gallicchio/ai_unleashes_chaos/docs/images/lorenz-bottom.png

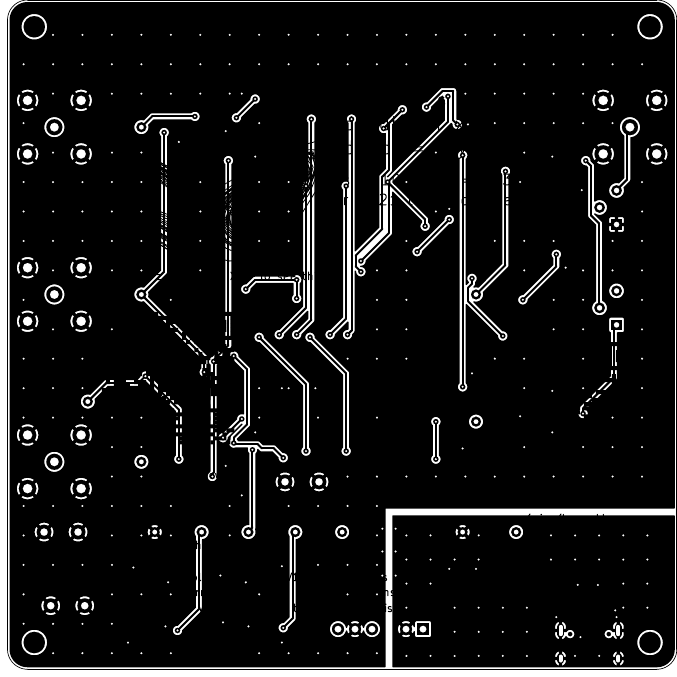
docs/images/lorenz-bottom.png
