gallicchio/ai_unleashes_chaos/docs/images/lorenz-silk-bottom.png

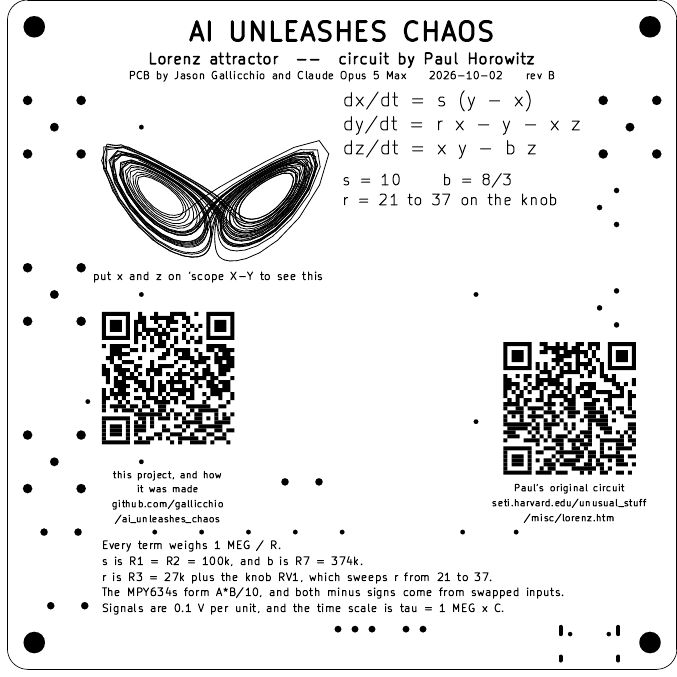
docs/images/lorenz-silk-bottom.png
