gallicchio/ai_unleashes_chaos/docs/images/lorenz-silk-top.png

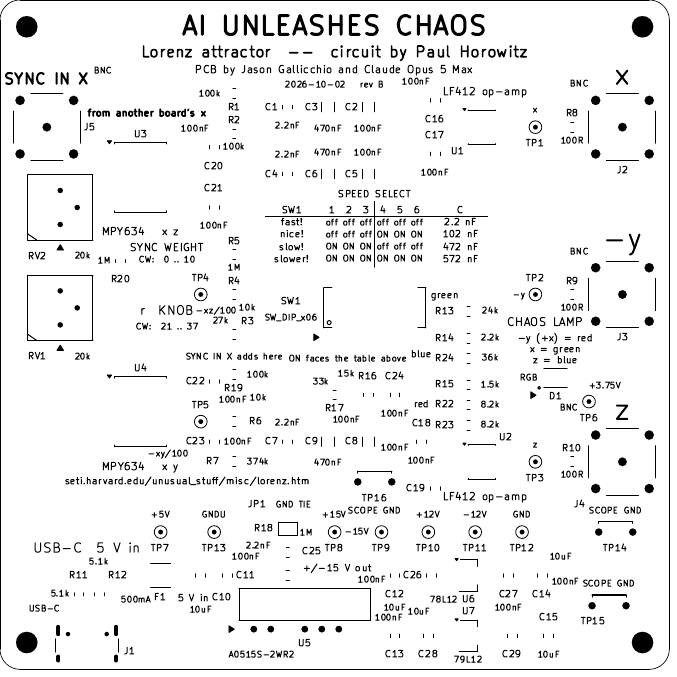
docs/images/lorenz-silk-top.png
