gallicchio/ai_unleashes_chaos/docs/images/lorenz-top.png

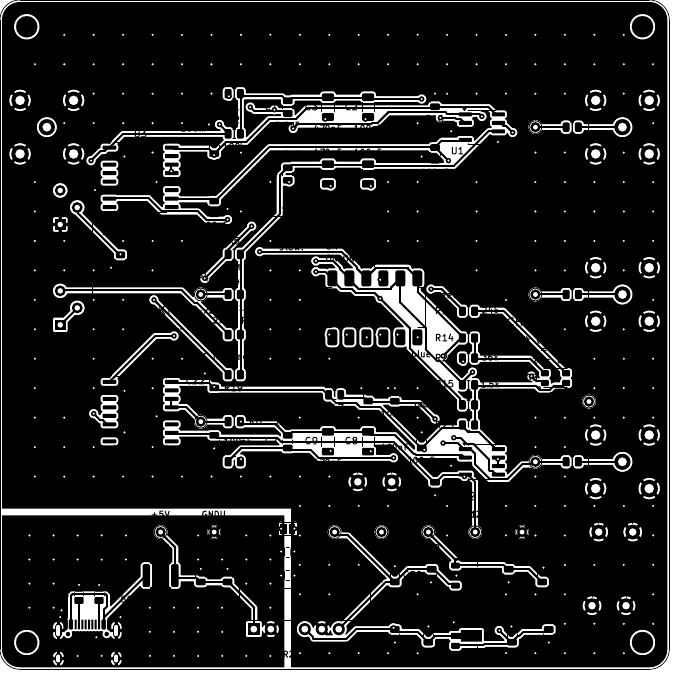
docs/images/lorenz-top.png
