gallicchio/ai_unleashes_chaos/docs/images/thumbnail_jason.png

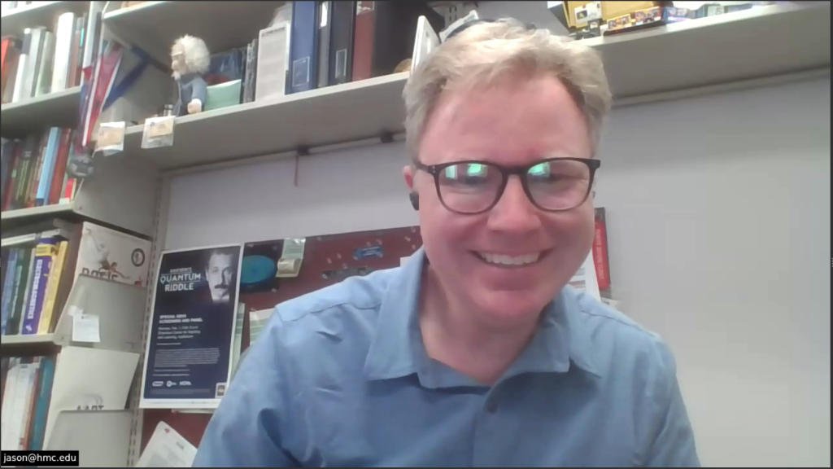
docs/images/thumbnail_jason.png
