gallicchio/ai_unleashes_chaos/docs/images/thumbnail_paul.png

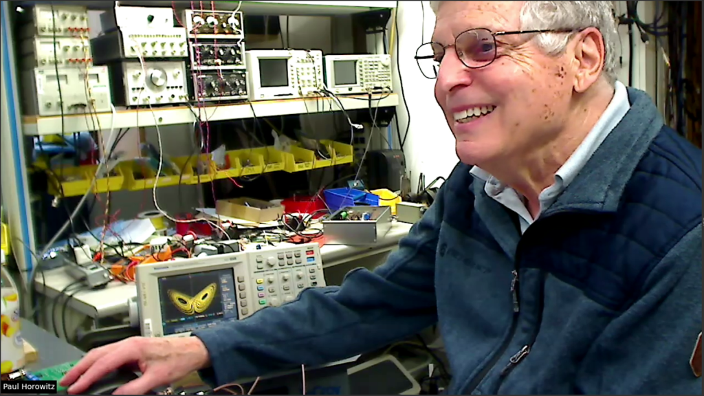
docs/images/thumbnail_paul.png
