gallicchio/ai_unleashes_chaos/docs/images/thumbnail_single.png

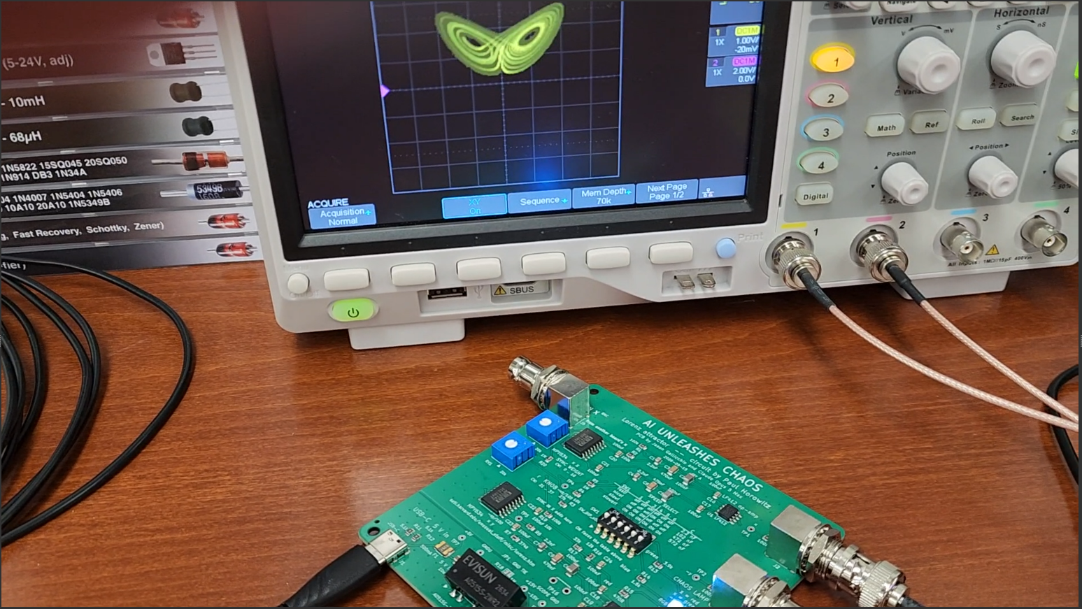
docs/images/thumbnail_single.png
