gallicchio/ai_unleashes_chaos/docs/images/thumbnail_sync.png

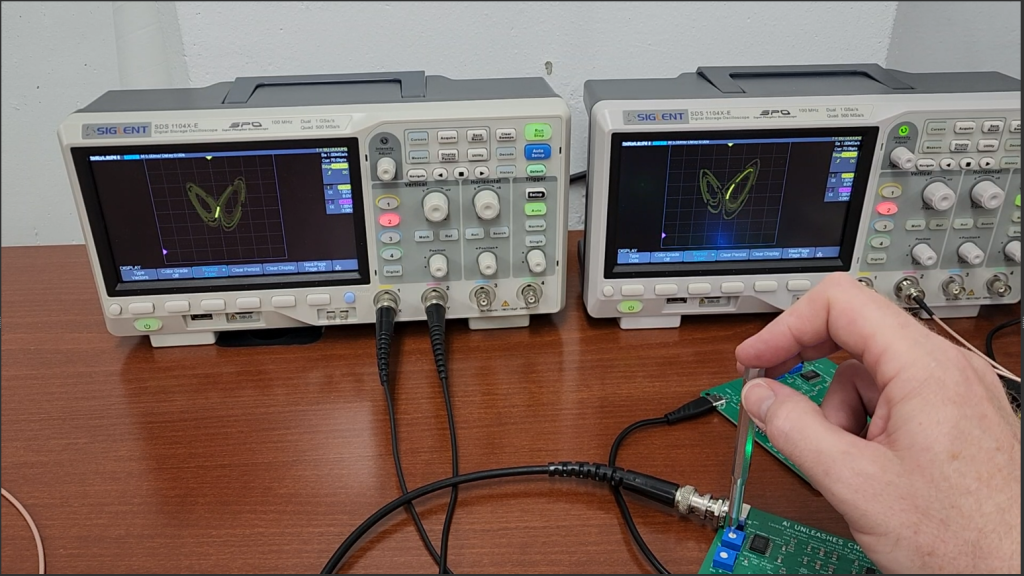
docs/images/thumbnail_sync.png
