gallicchio/ai_unleashes_chaos/docs/lamp/bestof/opt-038.png

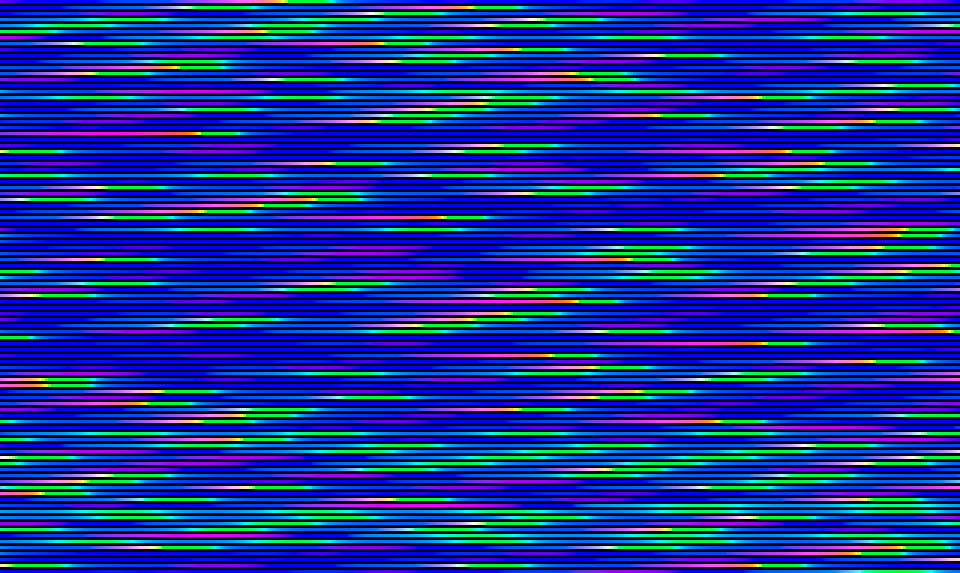
docs/lamp/bestof/opt-038.png
