gallicchio/ai_unleashes_chaos/docs/lamp/bestof/opt-054.png

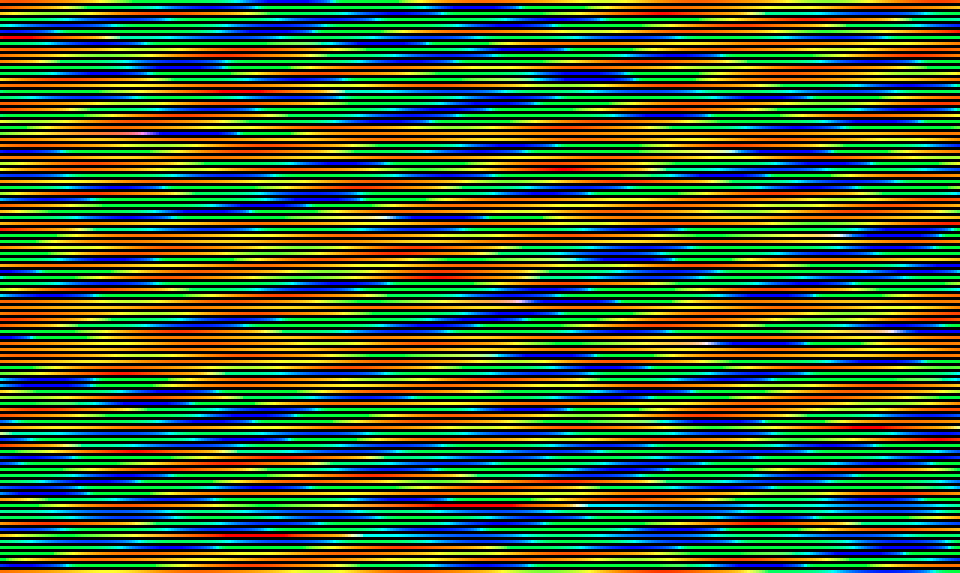
docs/lamp/bestof/opt-054.png
