gallicchio/ai_unleashes_chaos/docs/lamp/bestof/opt-065.png

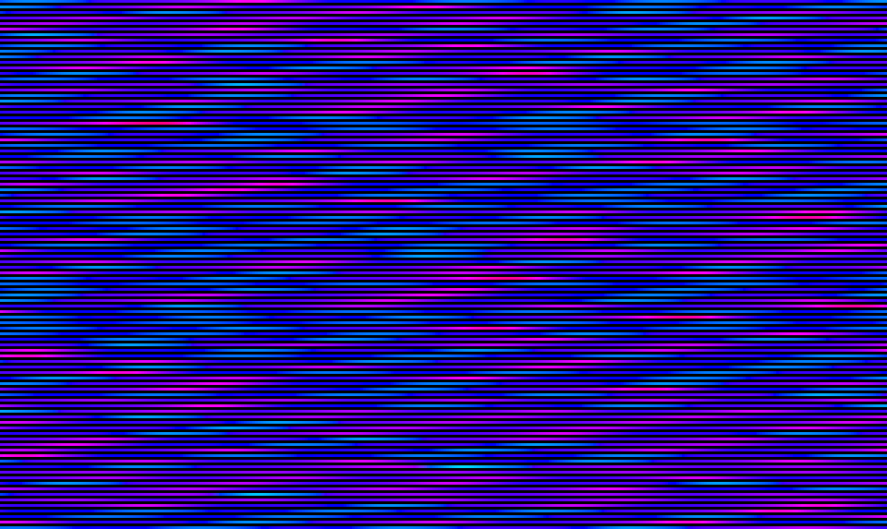
docs/lamp/bestof/opt-065.png
