gallicchio/ai_unleashes_chaos/docs/lamp/bestof/opt-072.png

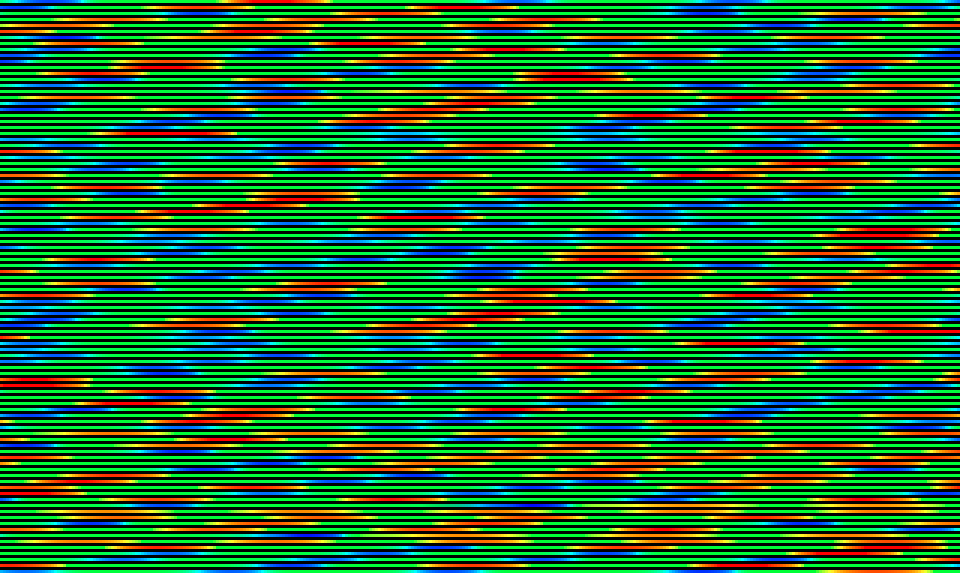
docs/lamp/bestof/opt-072.png
