gallicchio/ai_unleashes_chaos/docs/lamp/bestof/opt-088.png

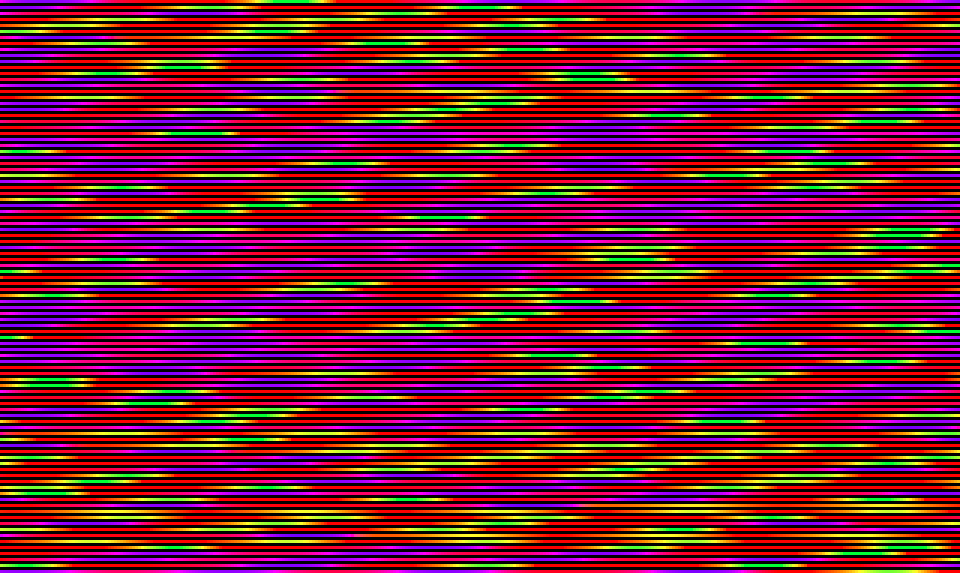
docs/lamp/bestof/opt-088.png
