gallicchio/ai_unleashes_chaos/docs/lamp/opt-001.png

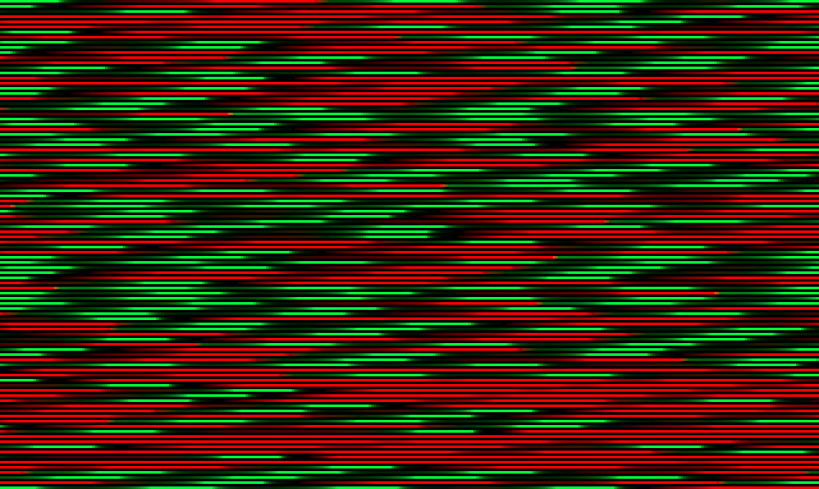
docs/lamp/opt-001.png
