gallicchio/ai_unleashes_chaos/docs/lamp/opt-002.png

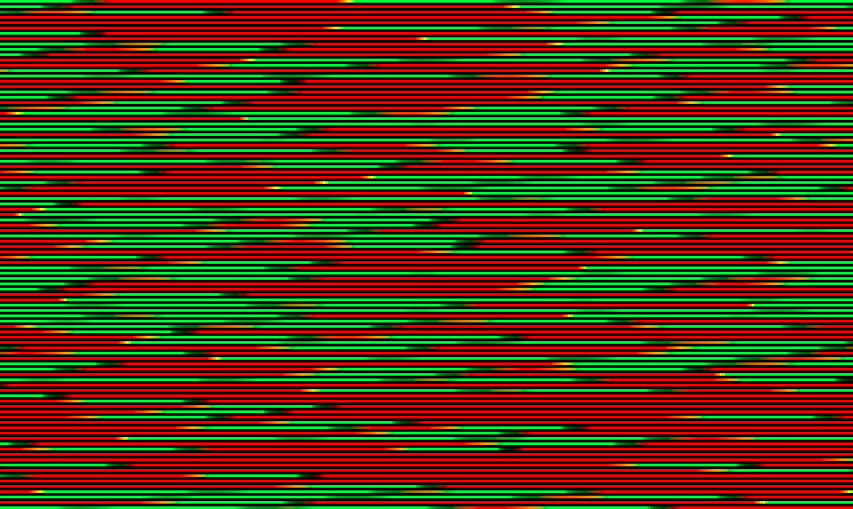
docs/lamp/opt-002.png
