gallicchio/ai_unleashes_chaos/docs/lamp/opt-003.png

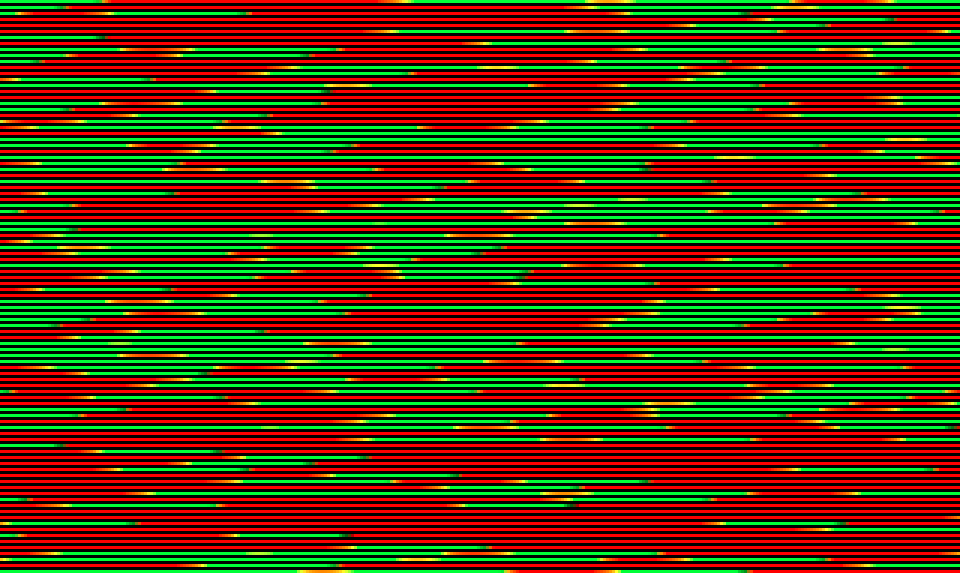
docs/lamp/opt-003.png
