gallicchio/ai_unleashes_chaos/docs/lamp/opt-004.png

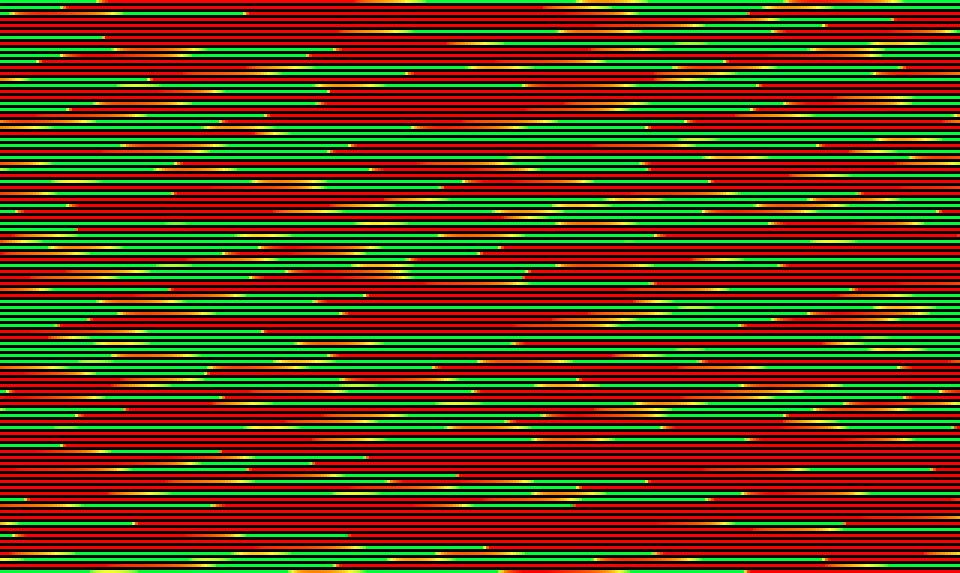
docs/lamp/opt-004.png
