gallicchio/ai_unleashes_chaos/docs/lamp/opt-006.png

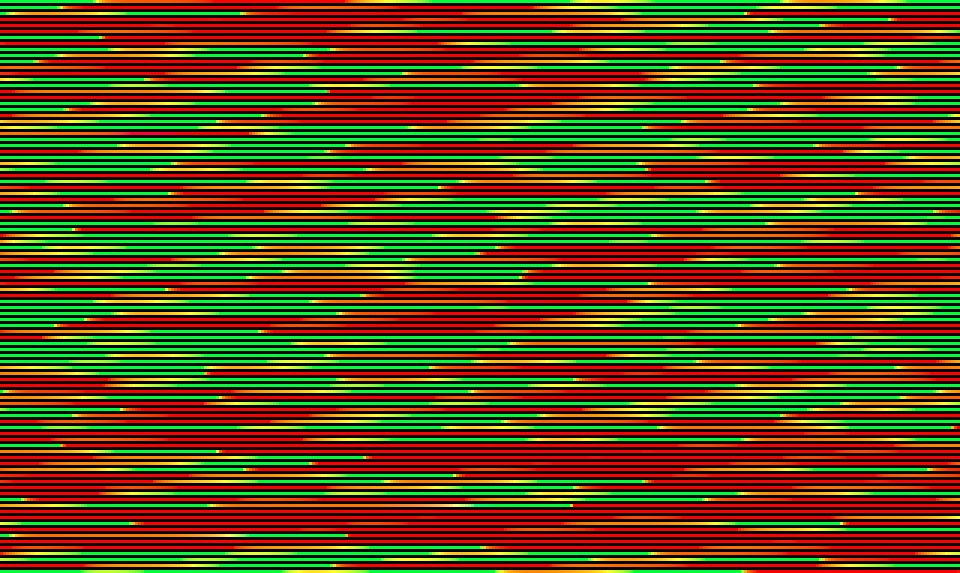
docs/lamp/opt-006.png
