gallicchio/ai_unleashes_chaos/docs/lamp/opt-007.png

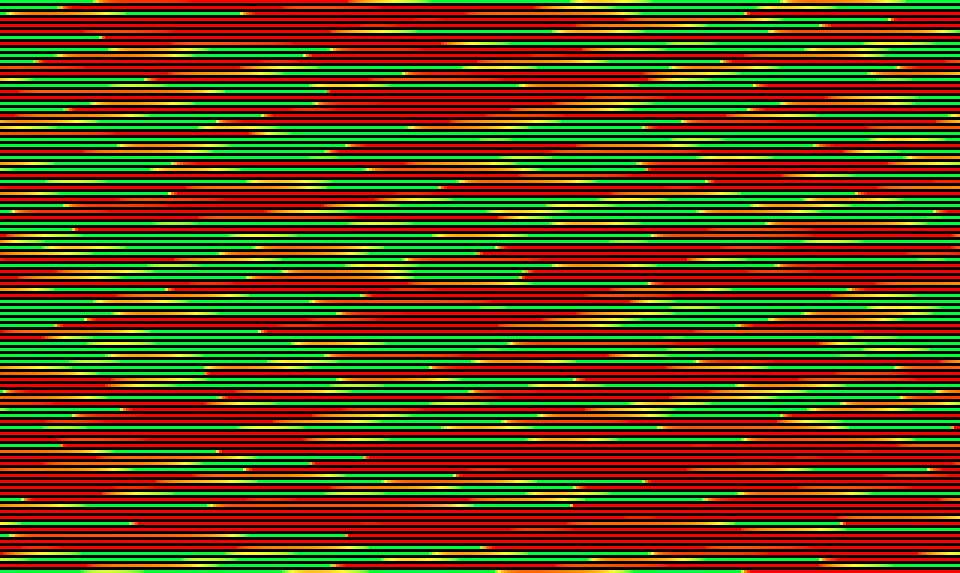
docs/lamp/opt-007.png
