gallicchio/ai_unleashes_chaos/docs/lamp/opt-008.png

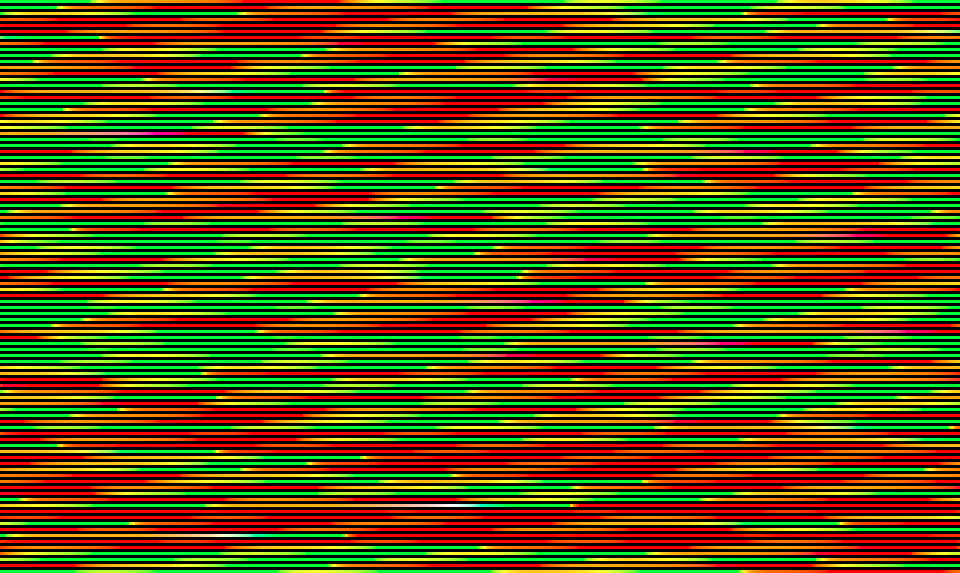
docs/lamp/opt-008.png
