gallicchio/ai_unleashes_chaos/docs/lamp/opt-010.png

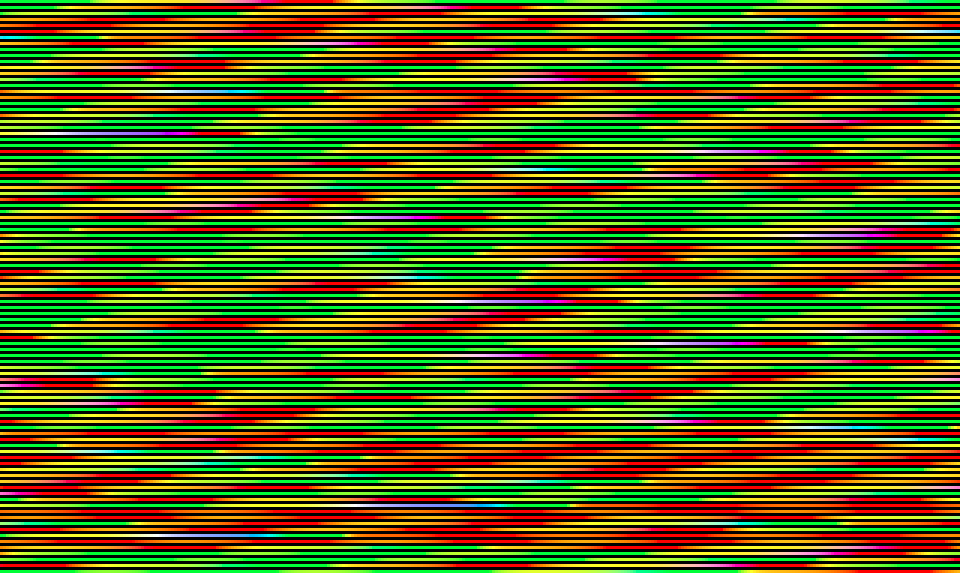
docs/lamp/opt-010.png
