gallicchio/ai_unleashes_chaos/docs/lamp/opt-011.png

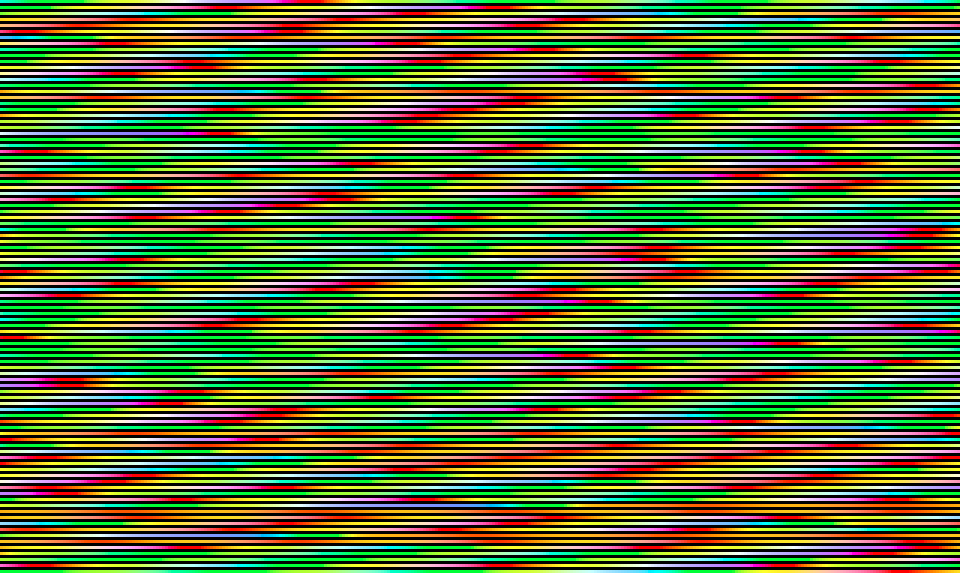
docs/lamp/opt-011.png
