gallicchio/ai_unleashes_chaos/docs/lamp/opt-012.png

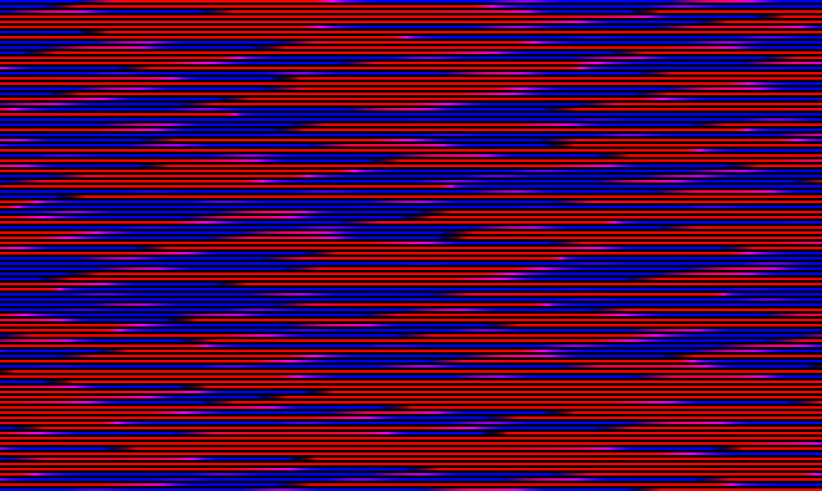
docs/lamp/opt-012.png
