gallicchio/ai_unleashes_chaos/docs/lamp/opt-013.png

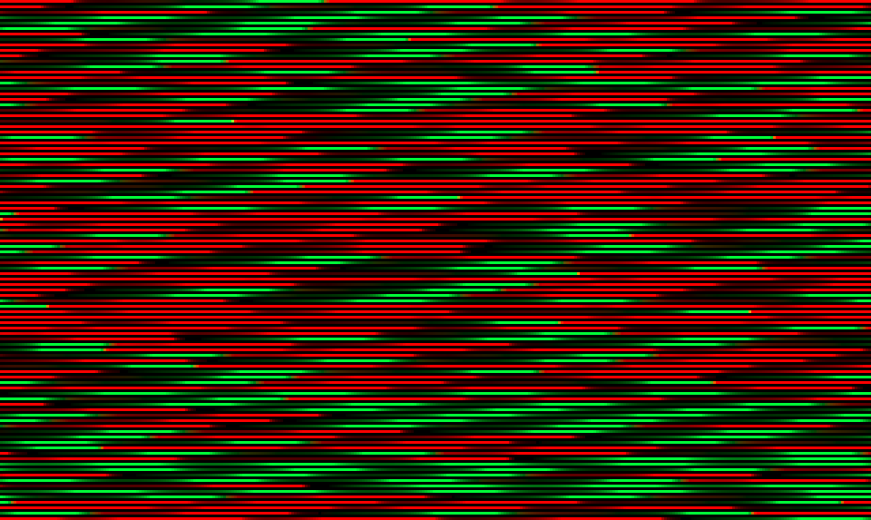
docs/lamp/opt-013.png
