gallicchio/ai_unleashes_chaos/docs/lamp/opt-014.png

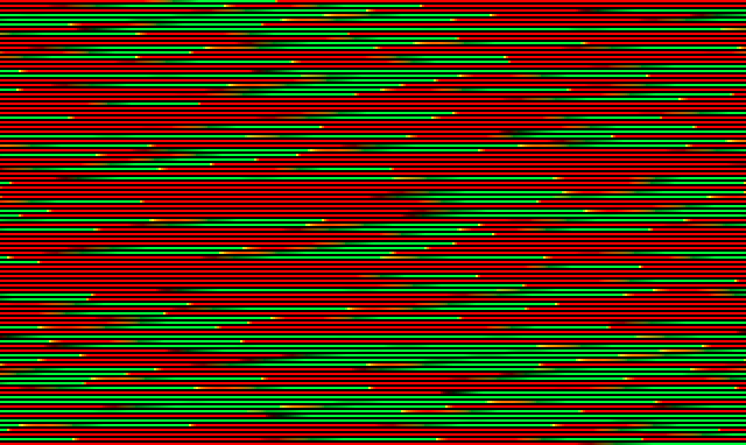
docs/lamp/opt-014.png
