gallicchio/ai_unleashes_chaos/docs/lamp/opt-015.png

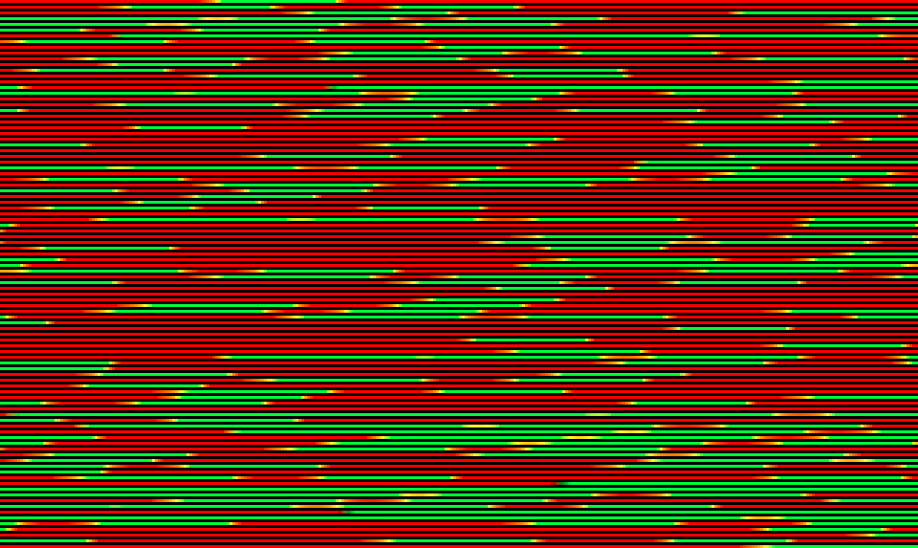
docs/lamp/opt-015.png
