gallicchio/ai_unleashes_chaos/docs/lamp/opt-016.png

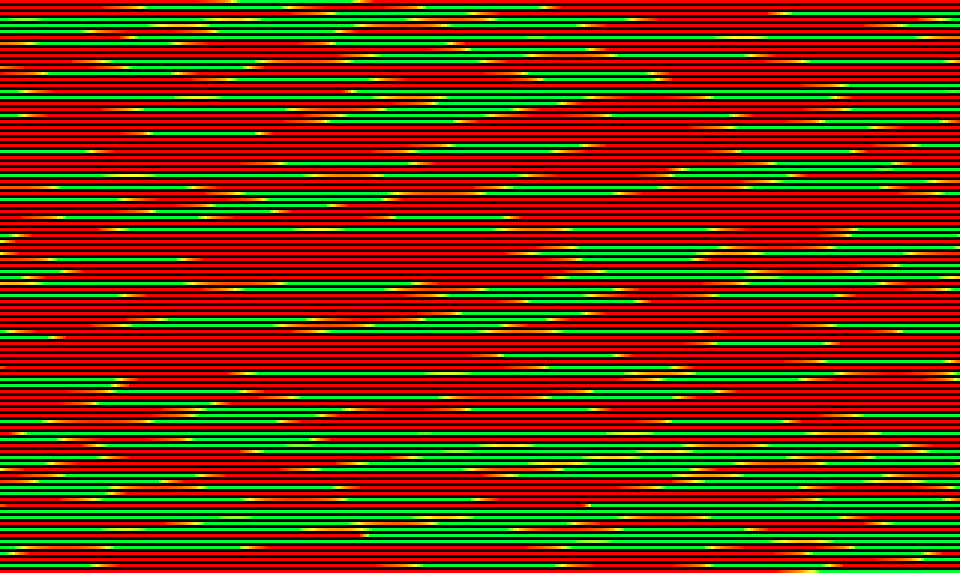
docs/lamp/opt-016.png
