gallicchio/ai_unleashes_chaos/docs/lamp/opt-017.png

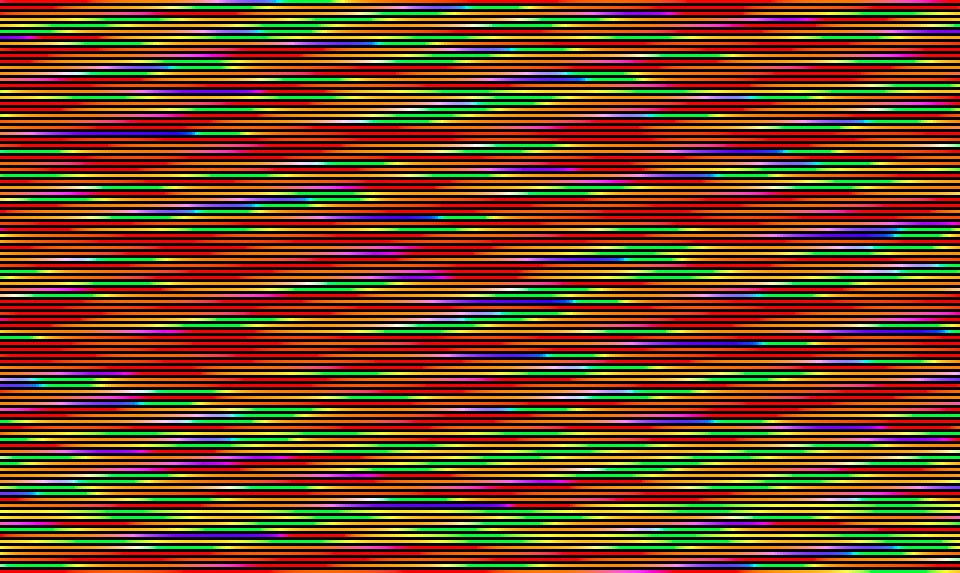
docs/lamp/opt-017.png
