gallicchio/ai_unleashes_chaos/docs/lamp/opt-018.png

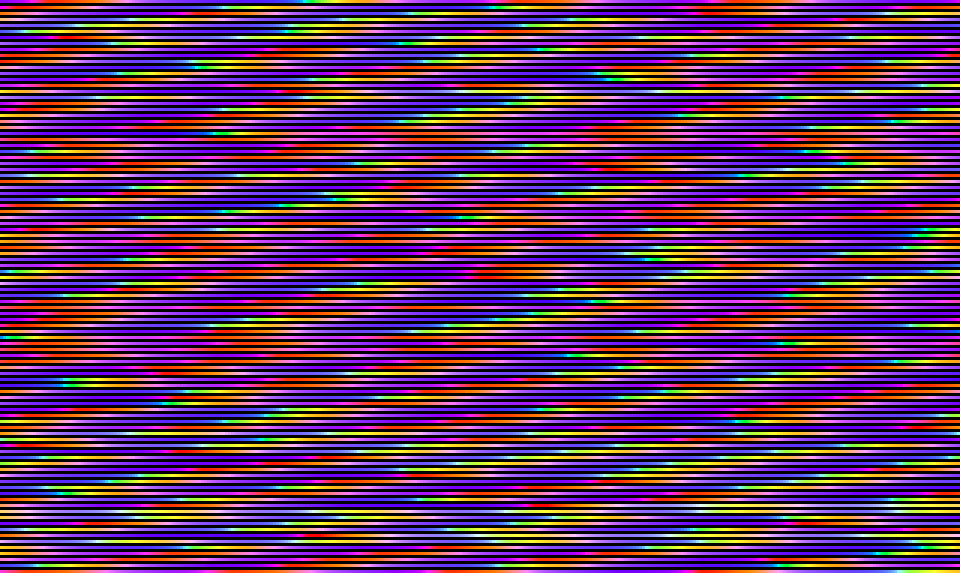
docs/lamp/opt-018.png
