gallicchio/ai_unleashes_chaos/docs/lamp/opt-019.png

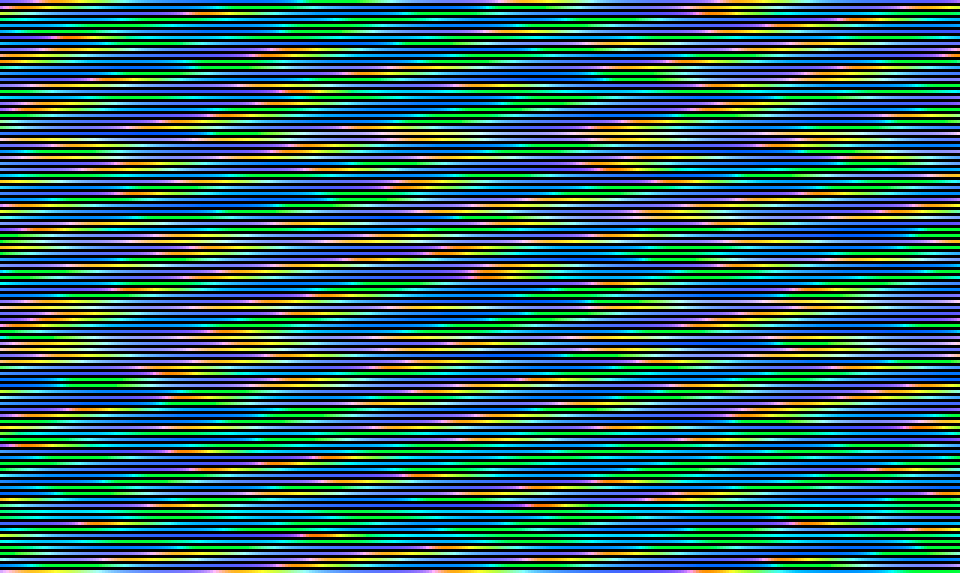
docs/lamp/opt-019.png
