gallicchio/ai_unleashes_chaos/docs/lamp/opt-020.png

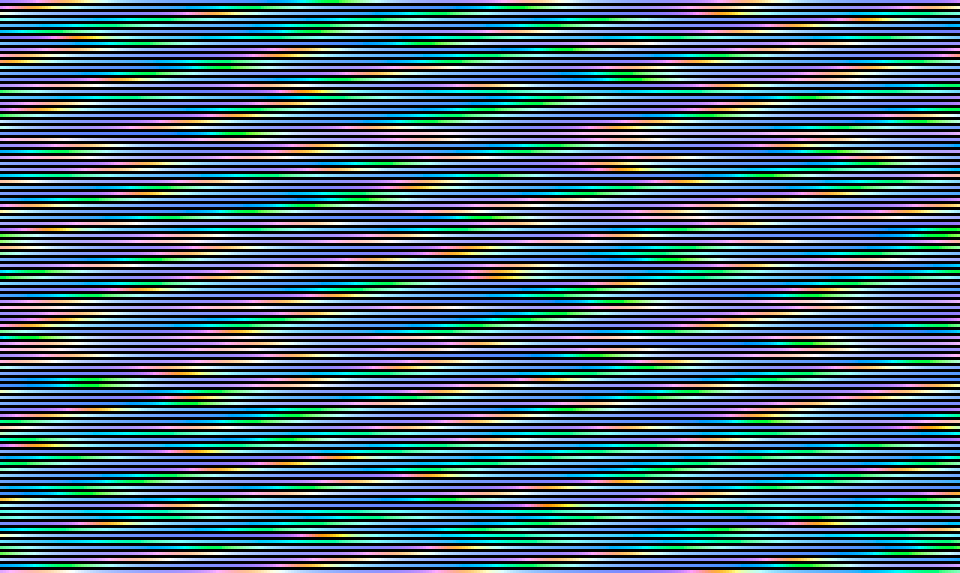
docs/lamp/opt-020.png
