gallicchio/ai_unleashes_chaos/docs/lamp/opt-021.png

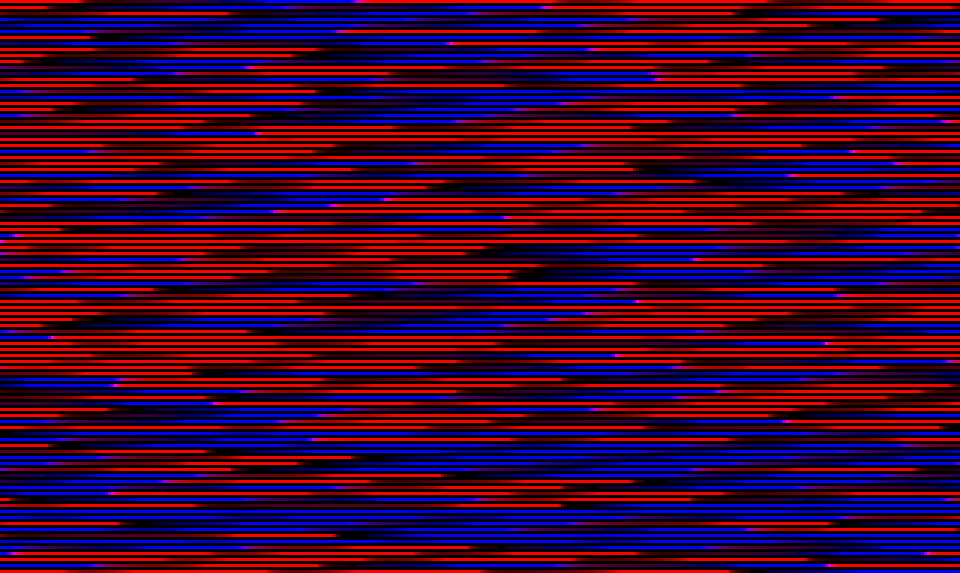
docs/lamp/opt-021.png
