gallicchio/ai_unleashes_chaos/docs/lamp/opt-022.png

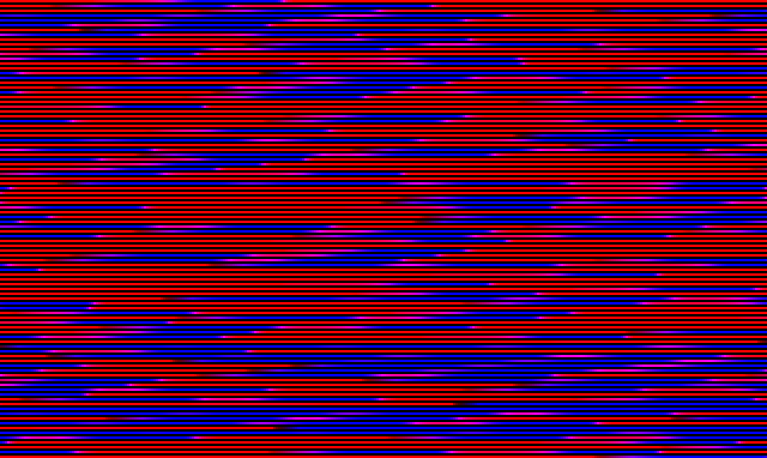
docs/lamp/opt-022.png
