gallicchio/ai_unleashes_chaos/docs/lamp/opt-023.png

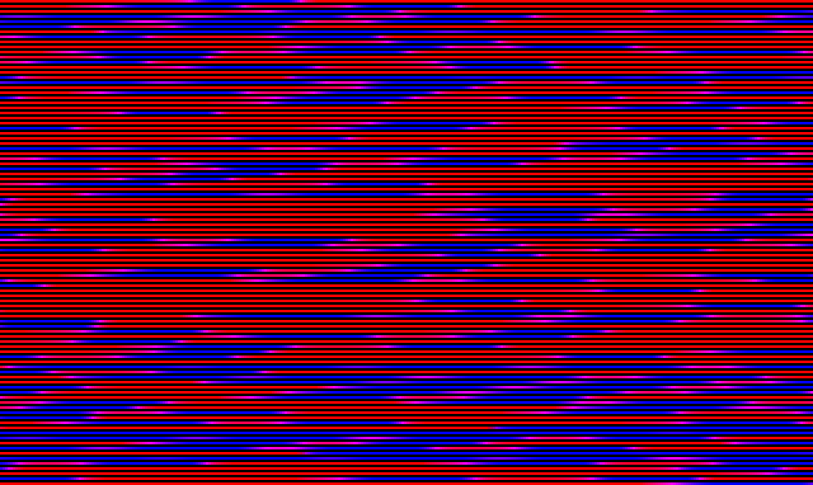
docs/lamp/opt-023.png
