gallicchio/ai_unleashes_chaos/docs/lamp/opt-024.png

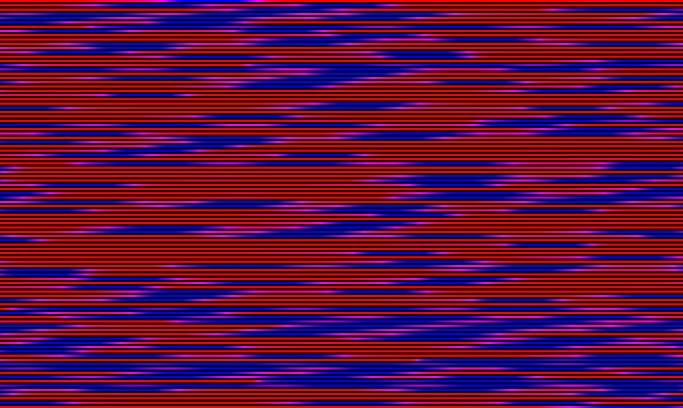
docs/lamp/opt-024.png
