gallicchio/ai_unleashes_chaos/docs/lamp/opt-025.png

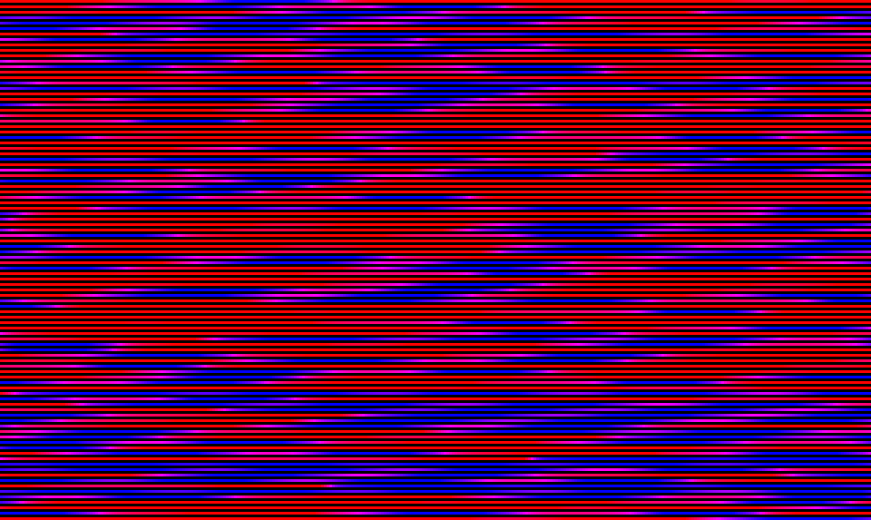
docs/lamp/opt-025.png
