gallicchio/ai_unleashes_chaos/docs/lamp/opt-027.png

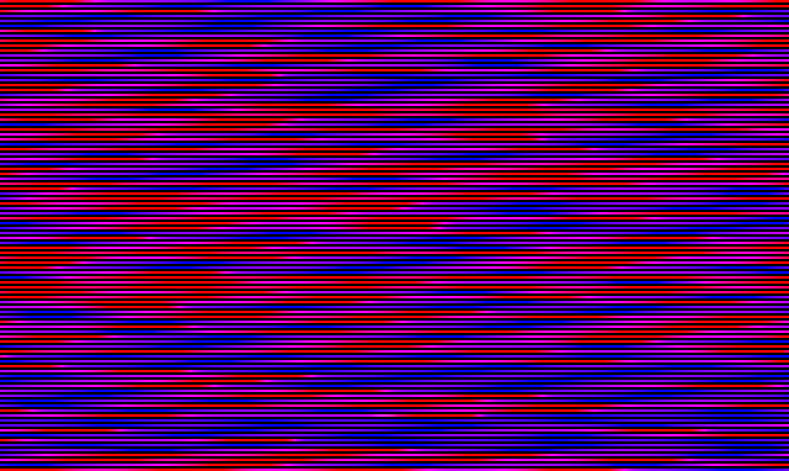
docs/lamp/opt-027.png
