gallicchio/ai_unleashes_chaos/docs/lamp/opt-028.png

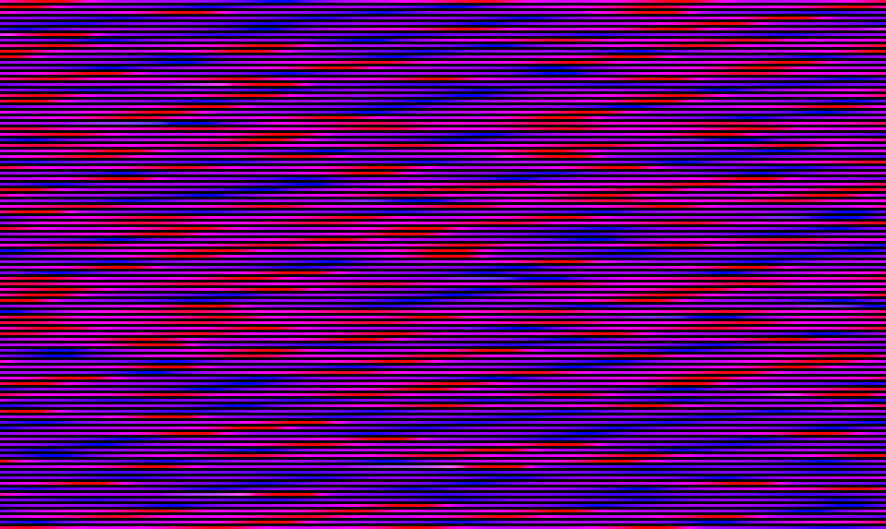
docs/lamp/opt-028.png
