gallicchio/ai_unleashes_chaos/docs/lamp/opt-029.png

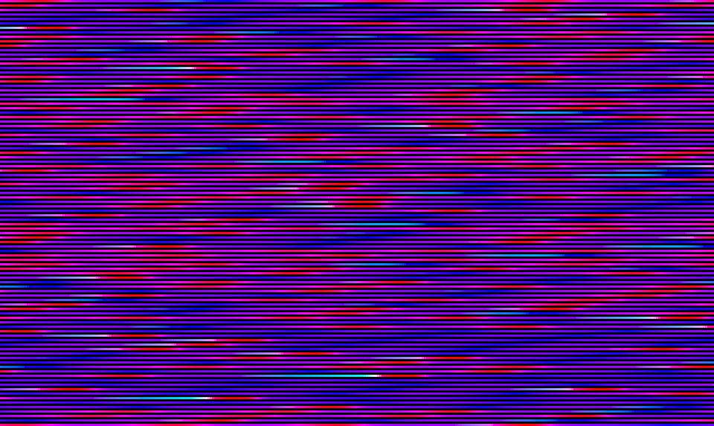
docs/lamp/opt-029.png
