gallicchio/ai_unleashes_chaos/docs/lamp/opt-030.png

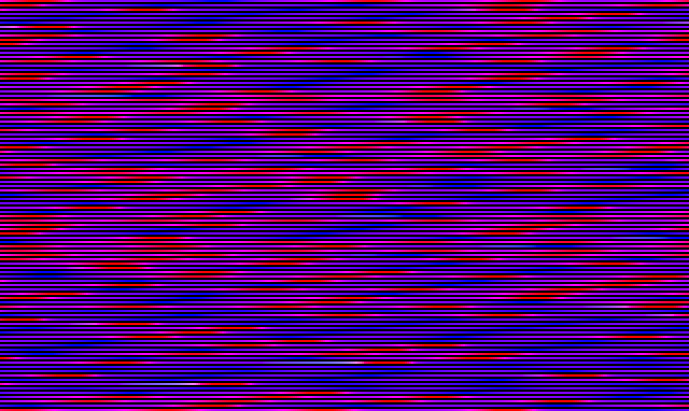
docs/lamp/opt-030.png
