gallicchio/ai_unleashes_chaos/docs/lamp/opt-031.png

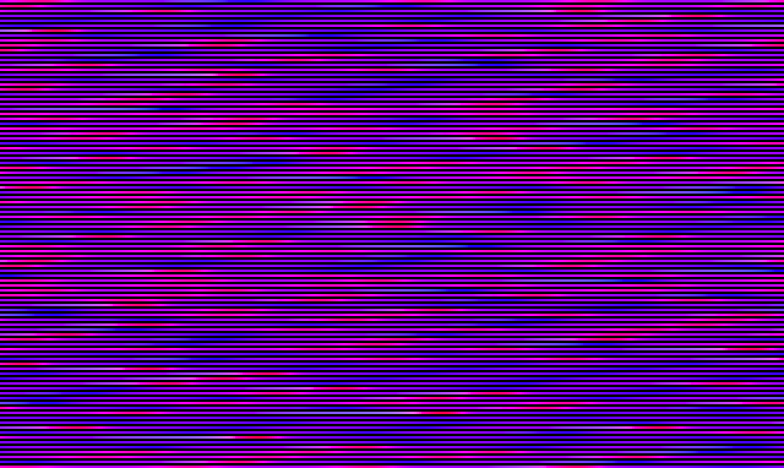
docs/lamp/opt-031.png
