gallicchio/ai_unleashes_chaos/docs/lamp/opt-032.png

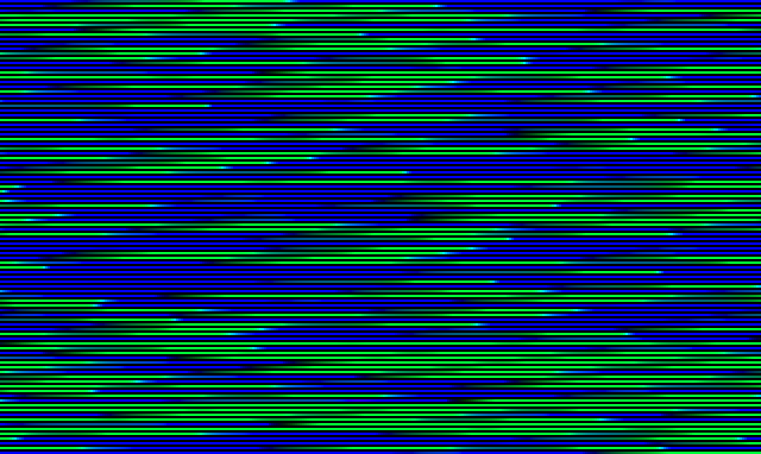
docs/lamp/opt-032.png
