gallicchio/ai_unleashes_chaos/docs/lamp/opt-033.png

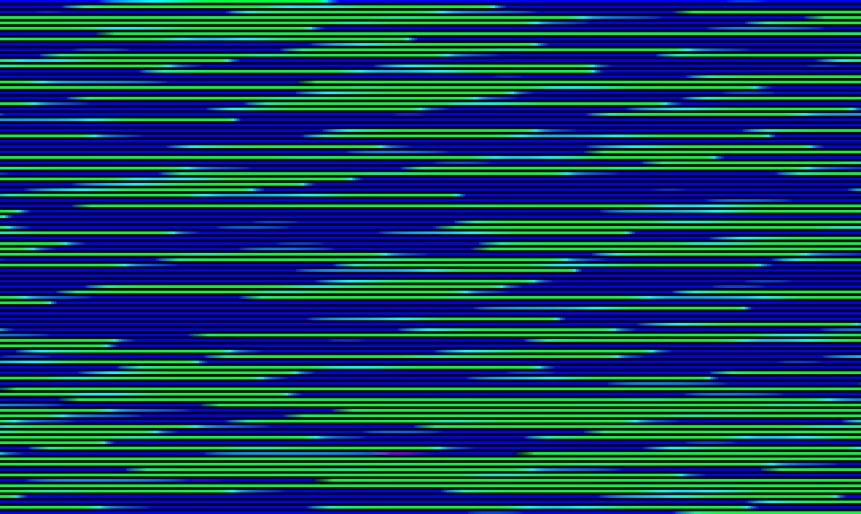
docs/lamp/opt-033.png
