gallicchio/ai_unleashes_chaos/docs/lamp/opt-035.png

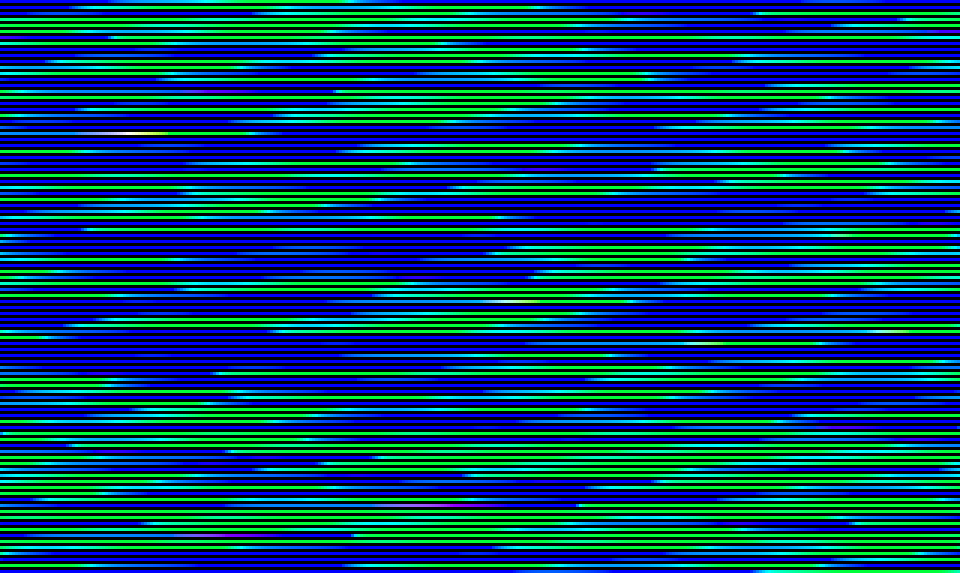
docs/lamp/opt-035.png
