gallicchio/ai_unleashes_chaos/docs/lamp/opt-036.png

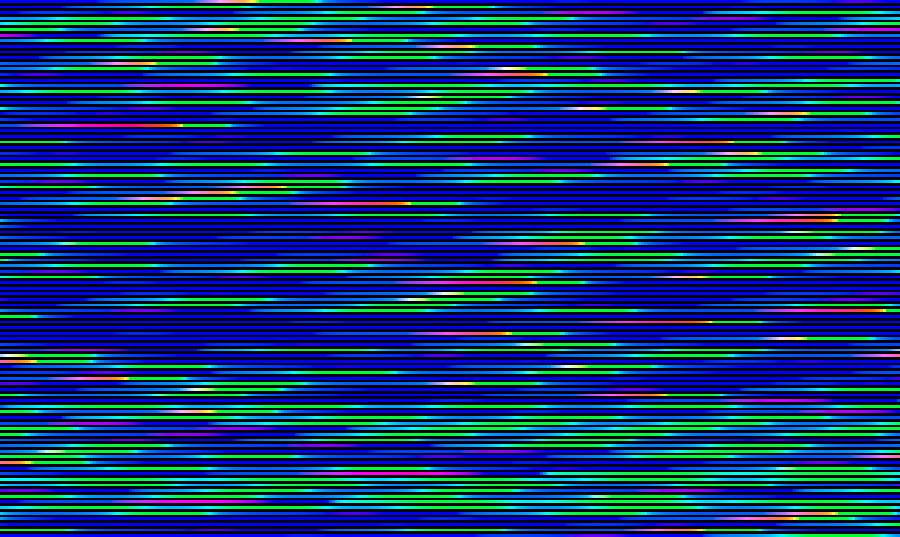
docs/lamp/opt-036.png
