gallicchio/ai_unleashes_chaos/docs/lamp/opt-037.png

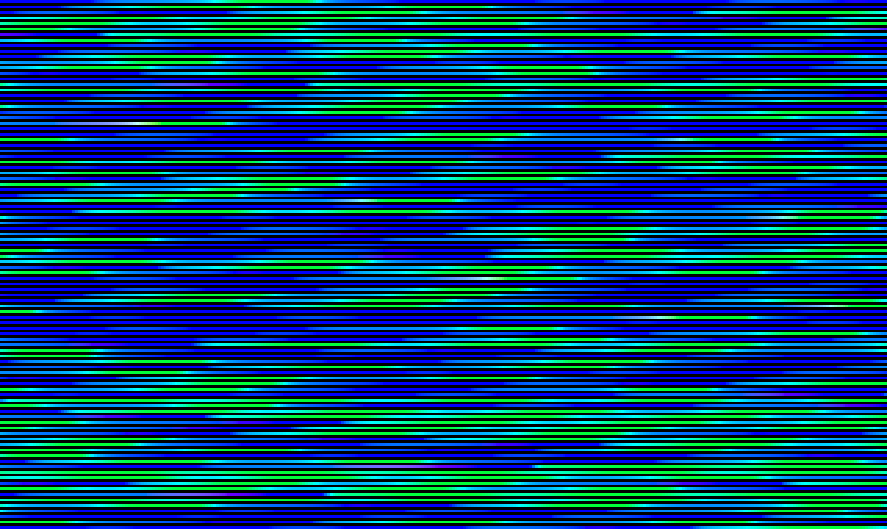
docs/lamp/opt-037.png
