gallicchio/ai_unleashes_chaos/docs/lamp/opt-040.png

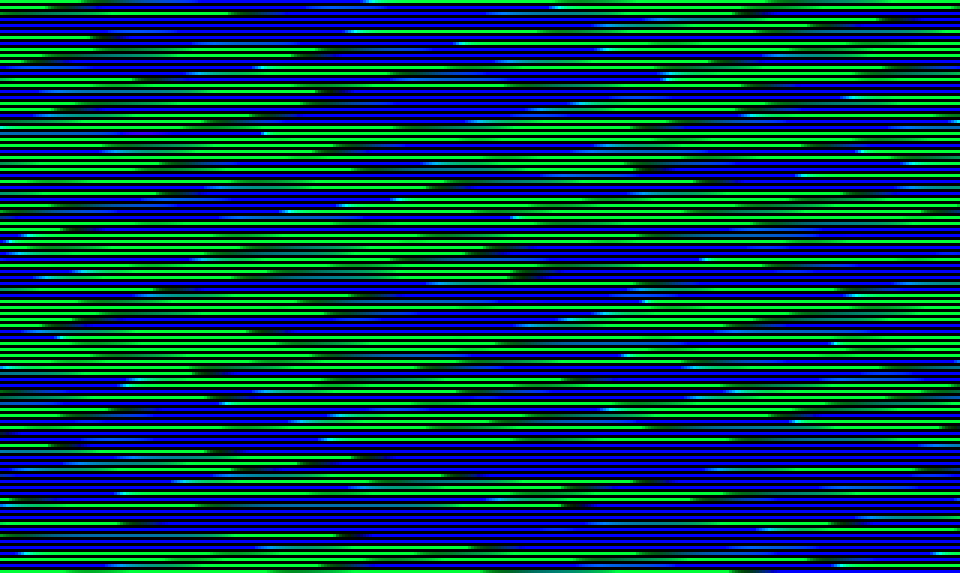
docs/lamp/opt-040.png
