gallicchio/ai_unleashes_chaos/docs/lamp/opt-041.png

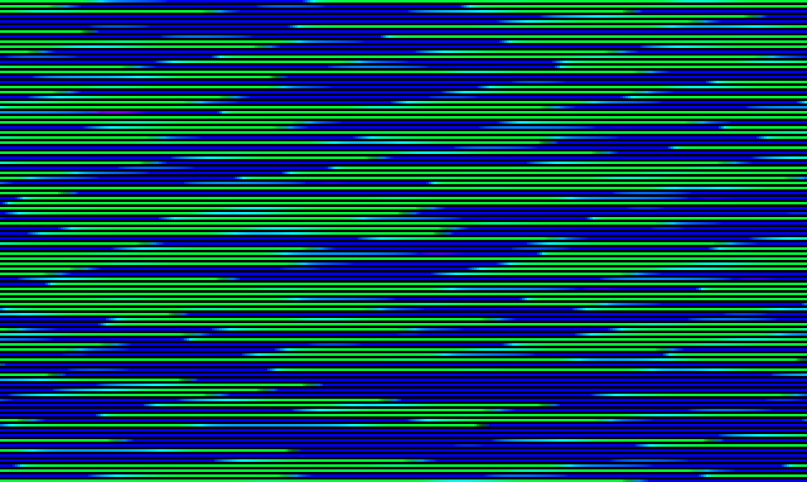
docs/lamp/opt-041.png
