gallicchio/ai_unleashes_chaos/docs/lamp/opt-044.png

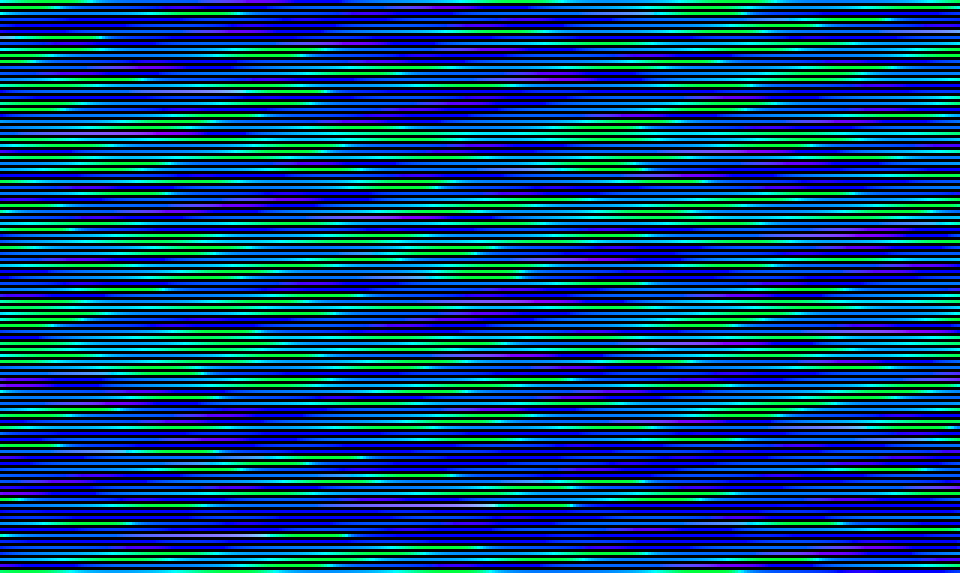
docs/lamp/opt-044.png
