gallicchio/ai_unleashes_chaos/docs/lamp/opt-045.png

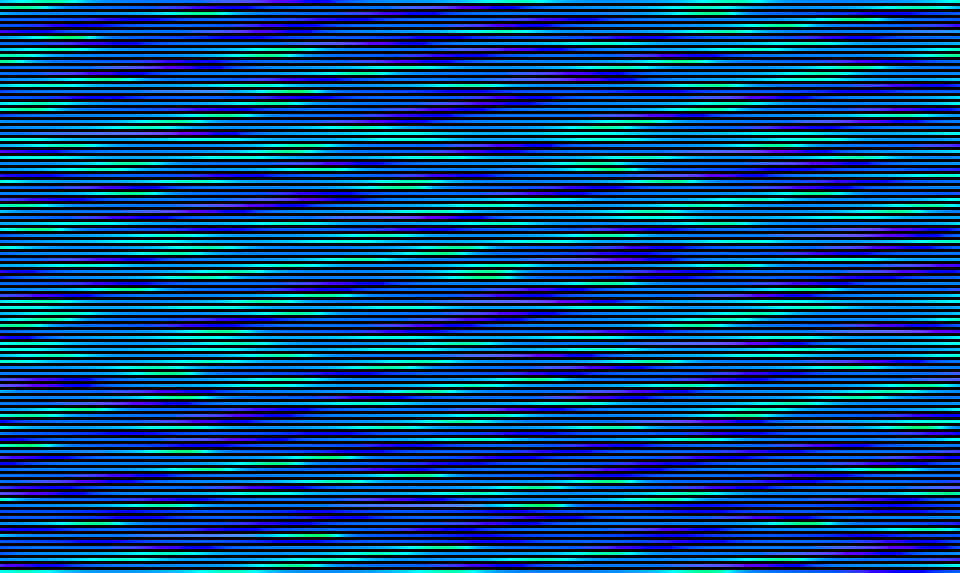
docs/lamp/opt-045.png
