gallicchio/ai_unleashes_chaos/docs/lamp/opt-046.png

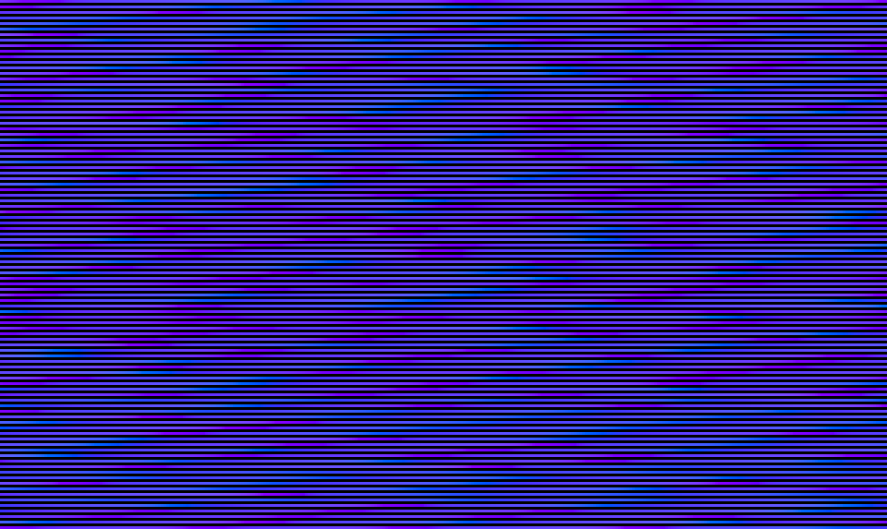
docs/lamp/opt-046.png
