gallicchio/ai_unleashes_chaos/docs/lamp/opt-047.png

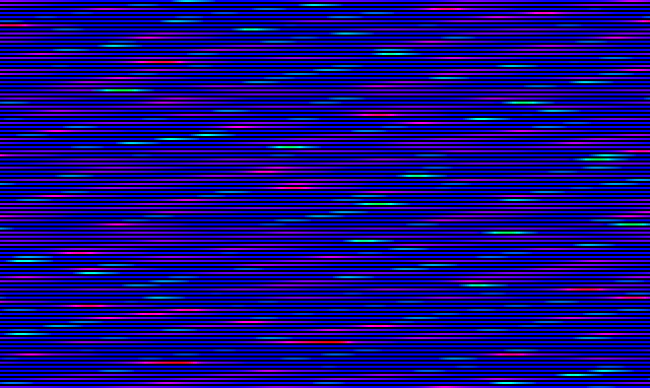
docs/lamp/opt-047.png
