gallicchio/ai_unleashes_chaos/docs/lamp/opt-048.png

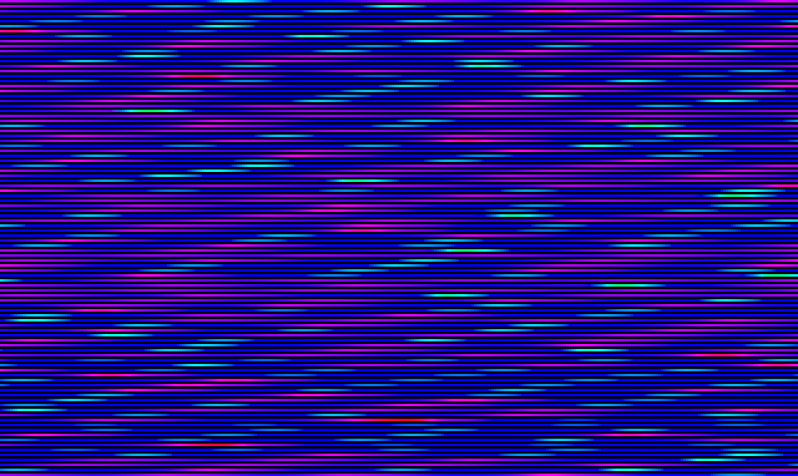
docs/lamp/opt-048.png
