gallicchio/ai_unleashes_chaos/docs/lamp/opt-049.png

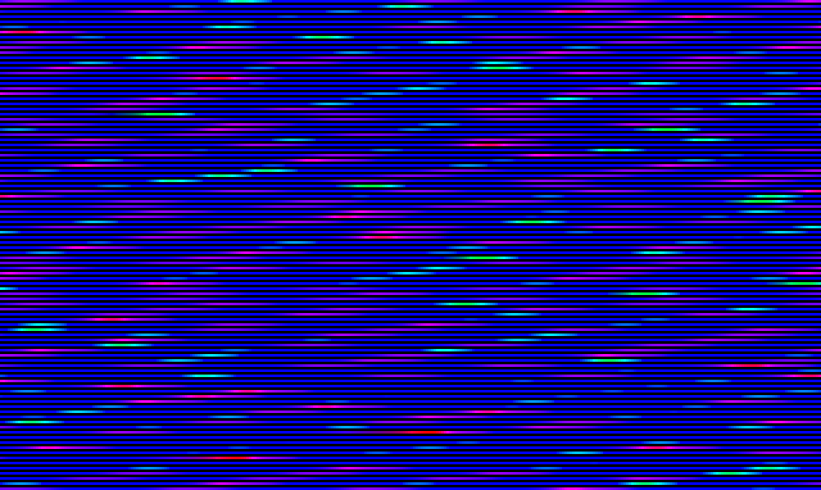
docs/lamp/opt-049.png
