gallicchio/ai_unleashes_chaos/docs/lamp/opt-050.png

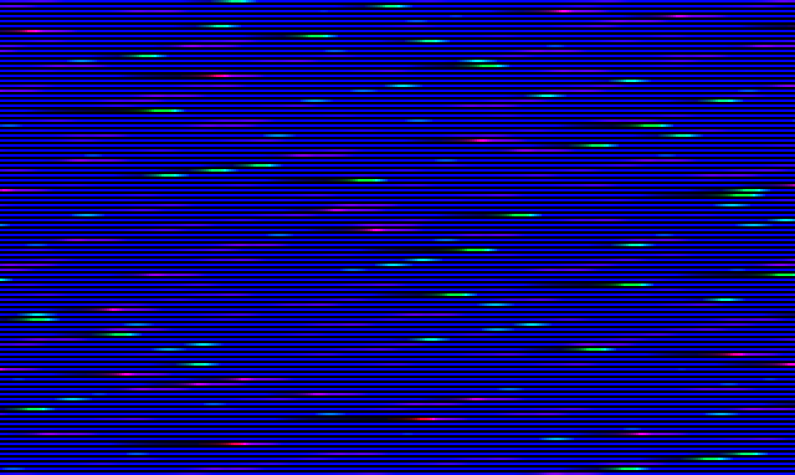
docs/lamp/opt-050.png
