gallicchio/ai_unleashes_chaos/docs/lamp/opt-051.png

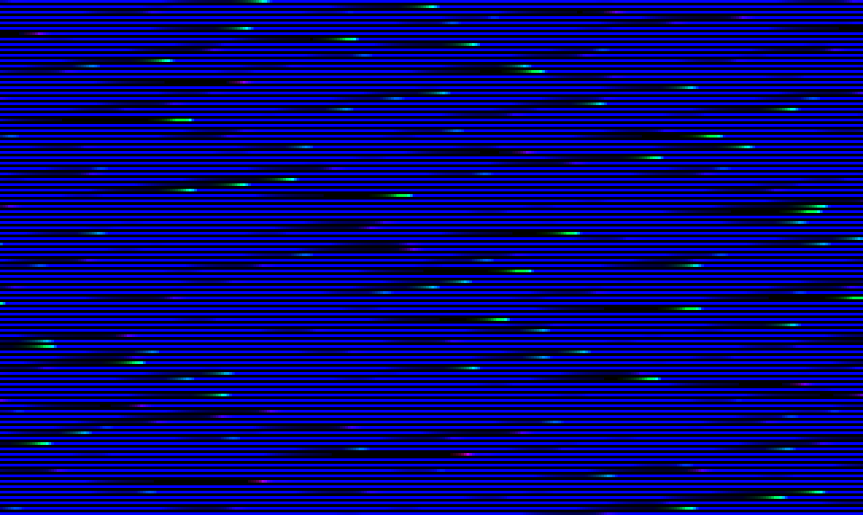
docs/lamp/opt-051.png
