gallicchio/ai_unleashes_chaos/docs/lamp/opt-052.png

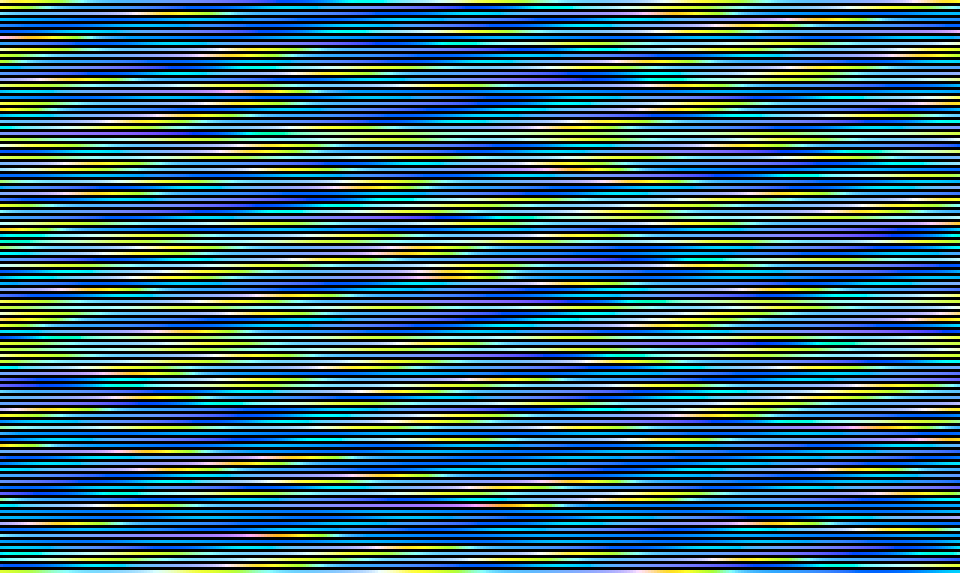
docs/lamp/opt-052.png
