gallicchio/ai_unleashes_chaos/docs/lamp/opt-053.png

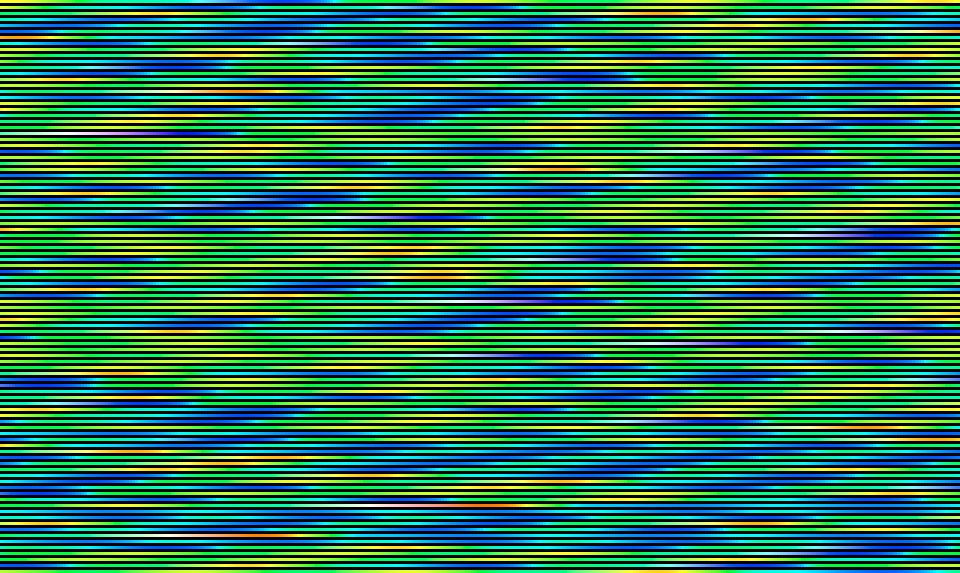
docs/lamp/opt-053.png
