gallicchio/ai_unleashes_chaos/docs/lamp/opt-055.png

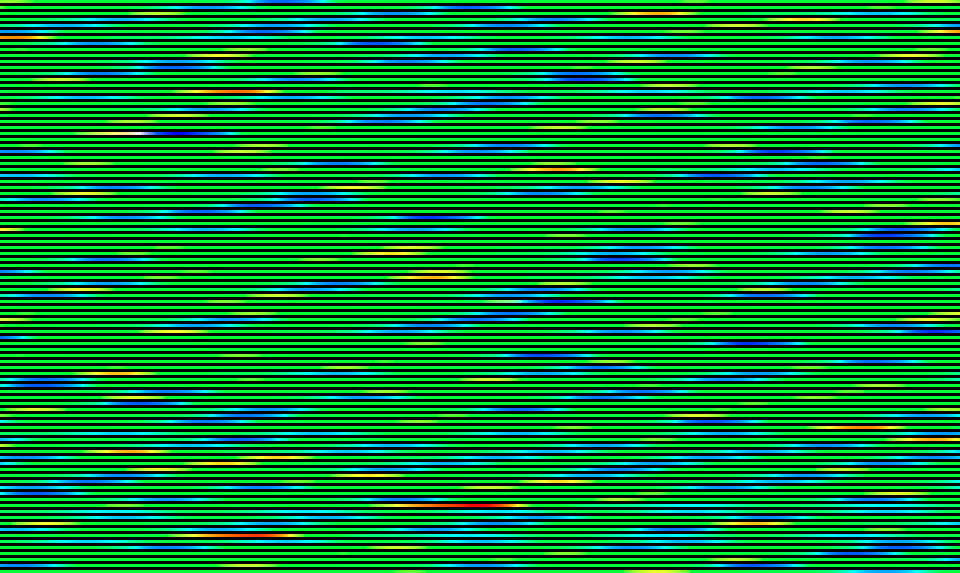
docs/lamp/opt-055.png
