gallicchio/ai_unleashes_chaos/docs/lamp/opt-056.png

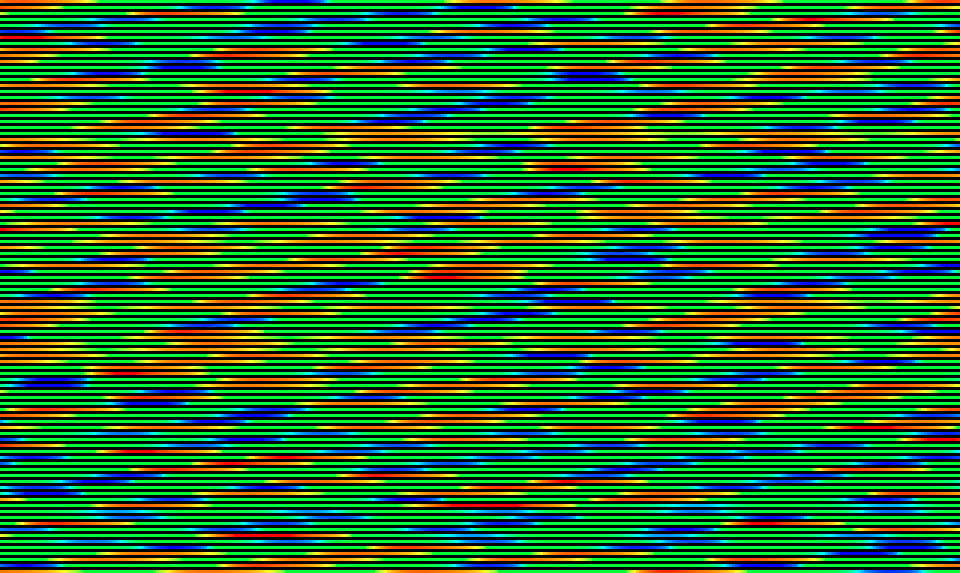
docs/lamp/opt-056.png
