gallicchio/ai_unleashes_chaos/docs/lamp/opt-057.png

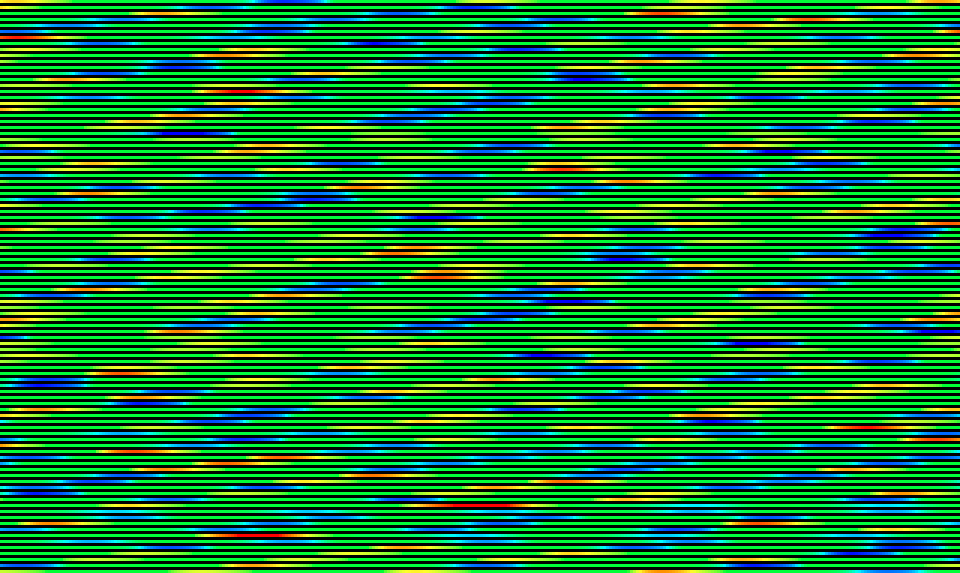
docs/lamp/opt-057.png
