gallicchio/ai_unleashes_chaos/docs/lamp/opt-058.png

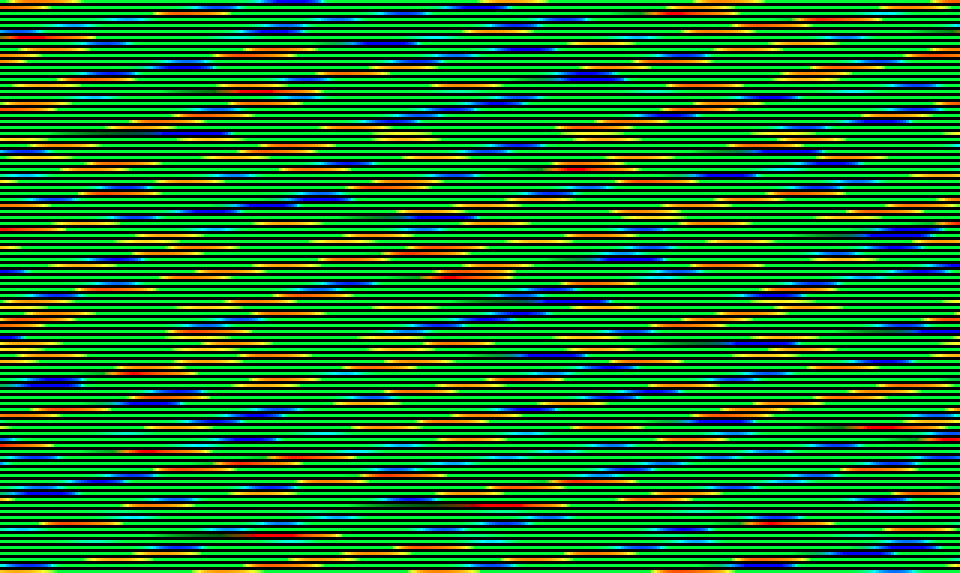
docs/lamp/opt-058.png
