gallicchio/ai_unleashes_chaos/docs/lamp/opt-059.png

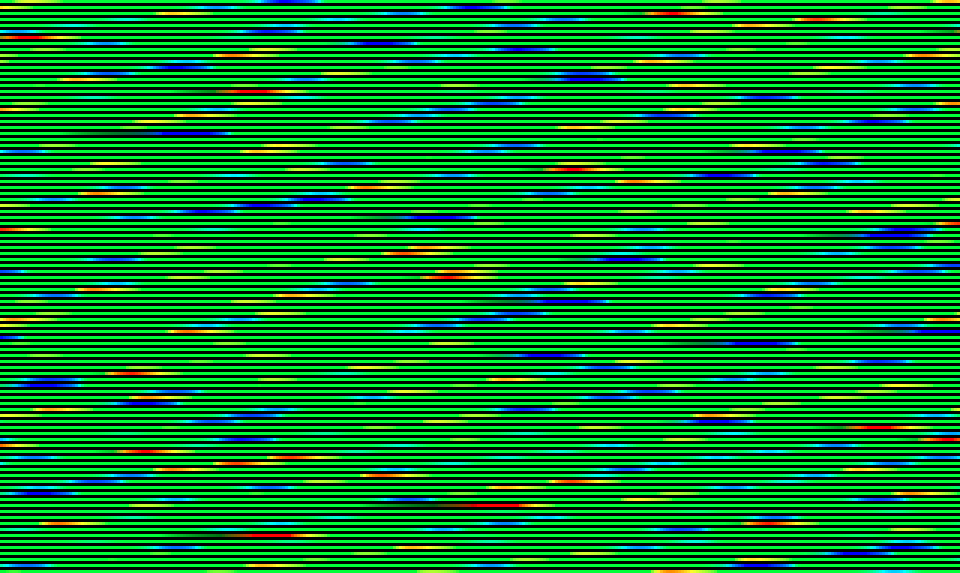
docs/lamp/opt-059.png
