gallicchio/ai_unleashes_chaos/docs/lamp/opt-060.png

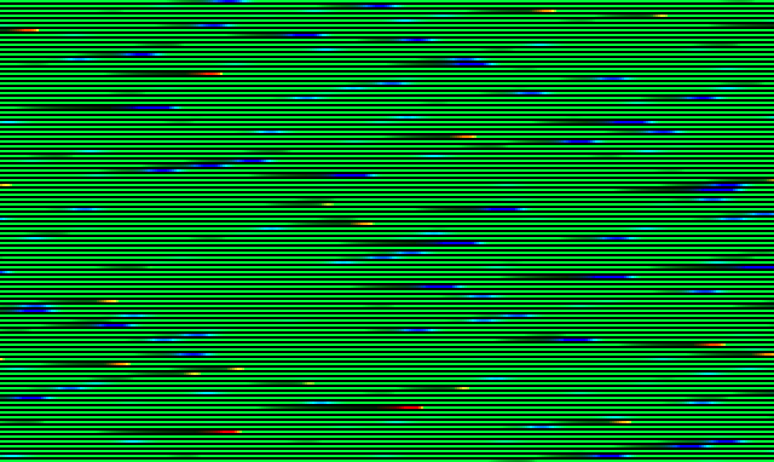
docs/lamp/opt-060.png
