gallicchio/ai_unleashes_chaos/docs/lamp/opt-061.png

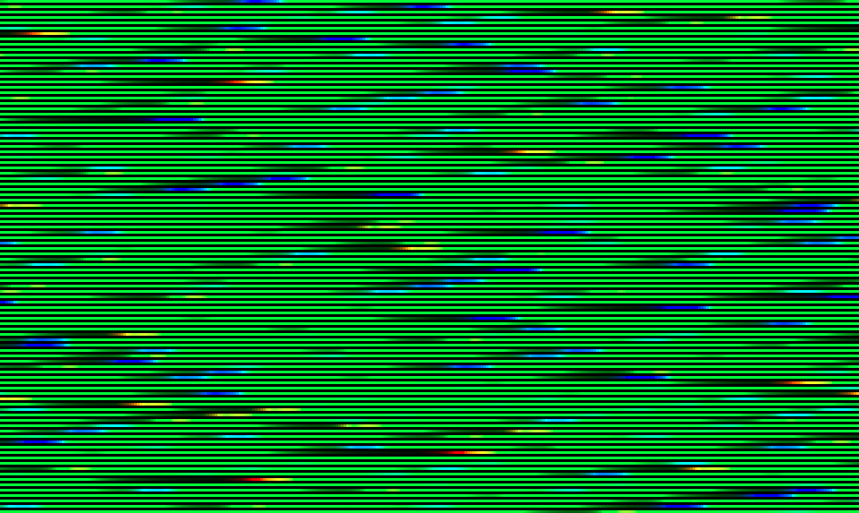
docs/lamp/opt-061.png
