gallicchio/ai_unleashes_chaos/docs/lamp/opt-062.png

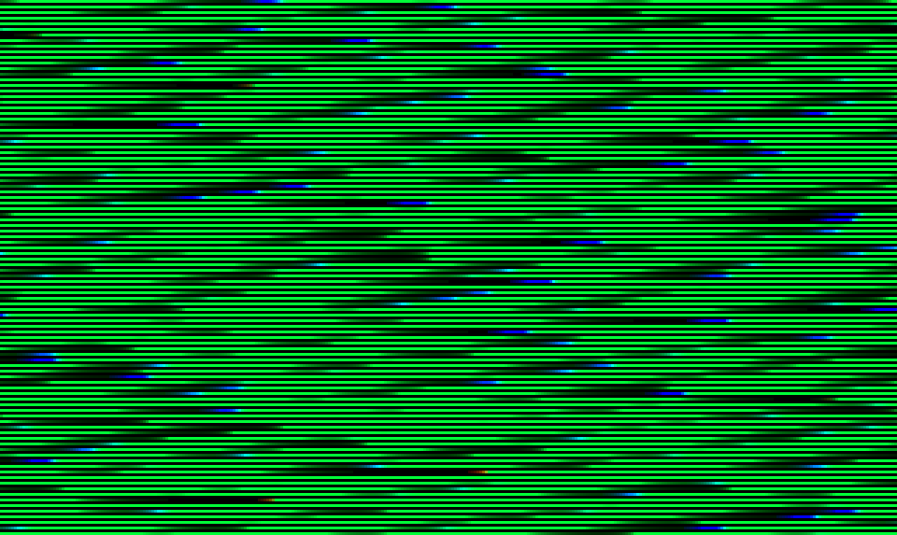
docs/lamp/opt-062.png
