gallicchio/ai_unleashes_chaos/docs/lamp/opt-063.png

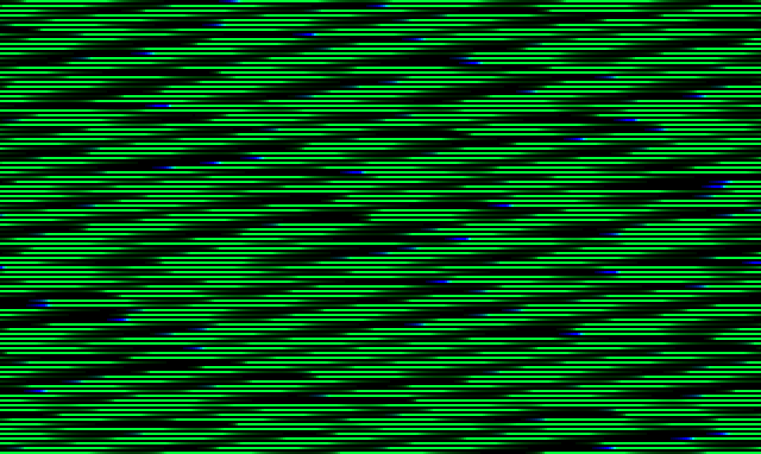
docs/lamp/opt-063.png
