gallicchio/ai_unleashes_chaos/docs/lamp/opt-064.png

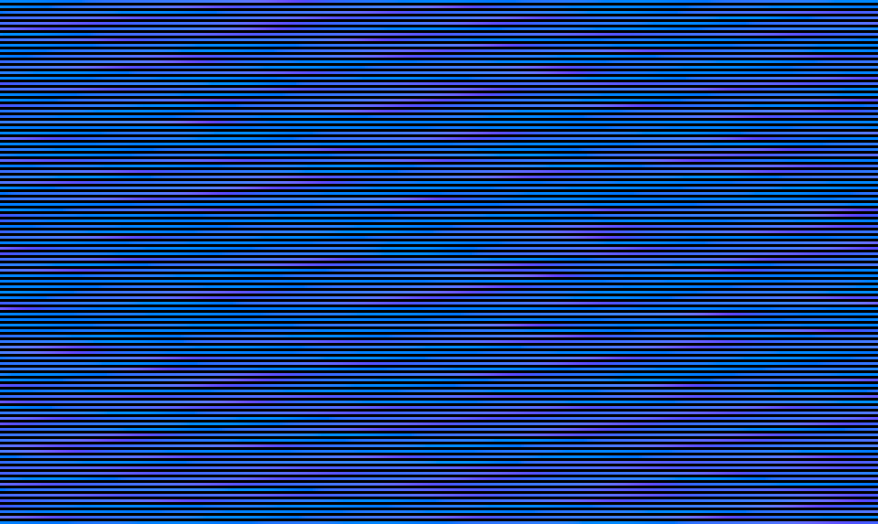
docs/lamp/opt-064.png
