gallicchio/ai_unleashes_chaos/docs/lamp/opt-066.png

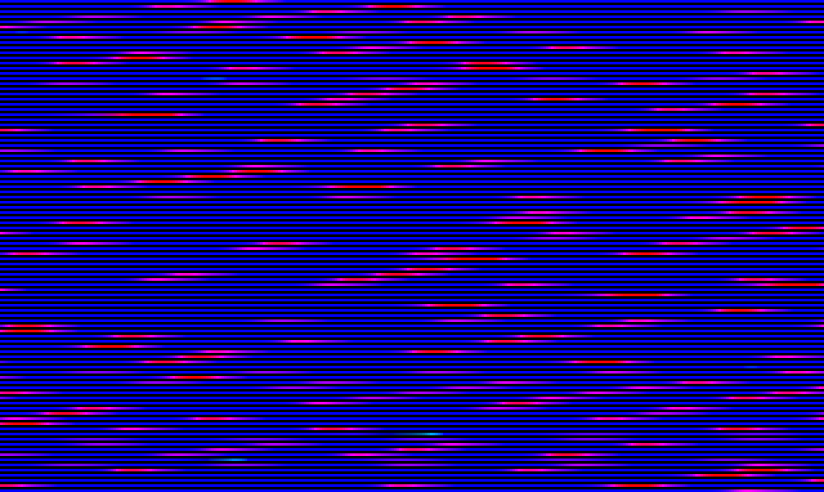
docs/lamp/opt-066.png
