gallicchio/ai_unleashes_chaos/docs/lamp/opt-067.png

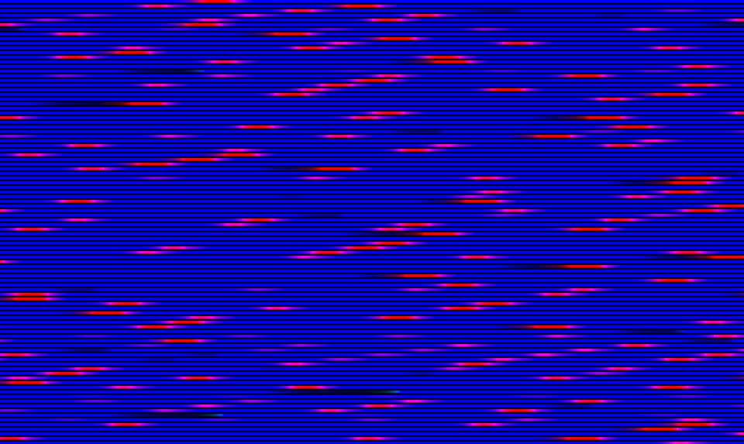
docs/lamp/opt-067.png
