gallicchio/ai_unleashes_chaos/docs/lamp/opt-068.png

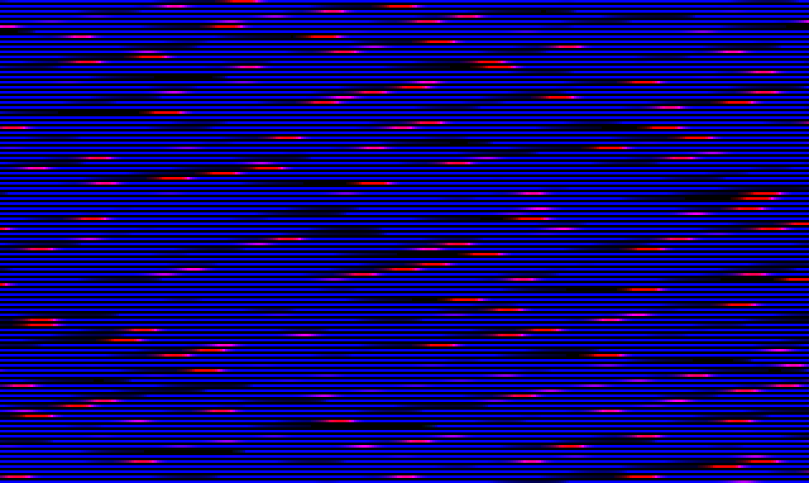
docs/lamp/opt-068.png
