gallicchio/ai_unleashes_chaos/docs/lamp/opt-069.png

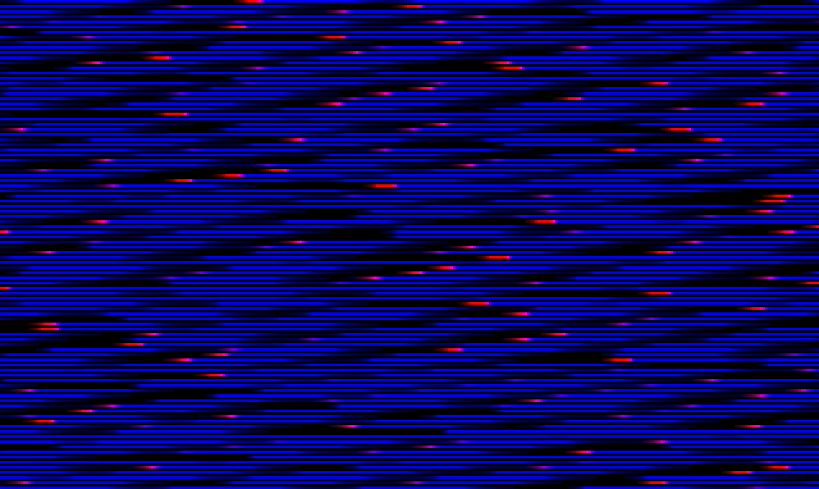
docs/lamp/opt-069.png
