gallicchio/ai_unleashes_chaos/docs/lamp/opt-070.png

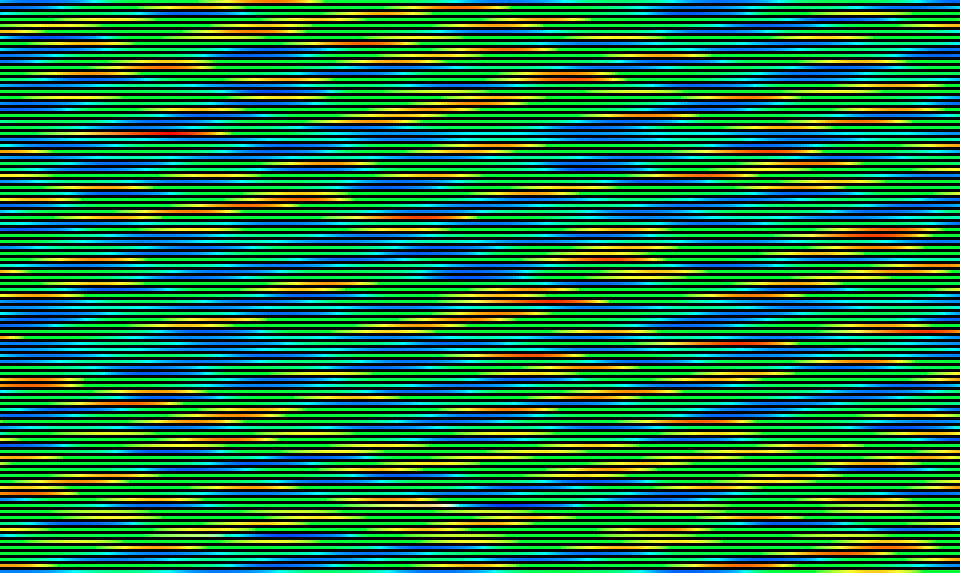
docs/lamp/opt-070.png
