gallicchio/ai_unleashes_chaos/docs/lamp/opt-071.png

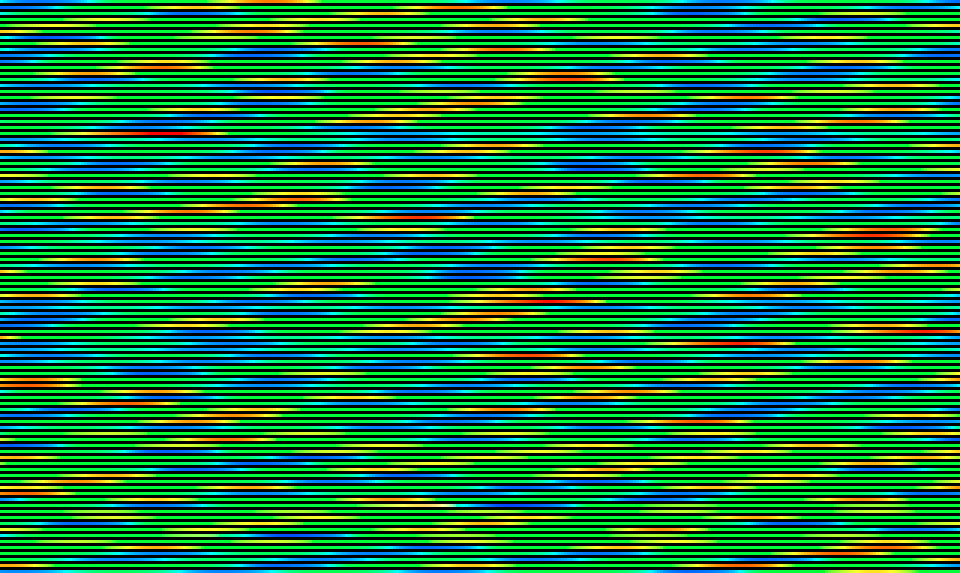
docs/lamp/opt-071.png
