gallicchio/ai_unleashes_chaos/docs/lamp/opt-073.png

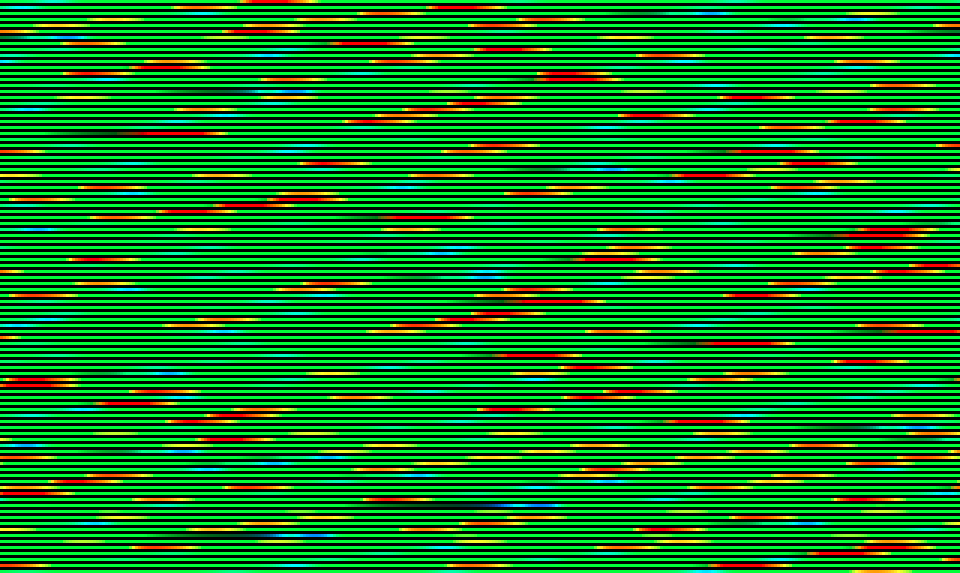
docs/lamp/opt-073.png
