gallicchio/ai_unleashes_chaos/docs/lamp/opt-075.png

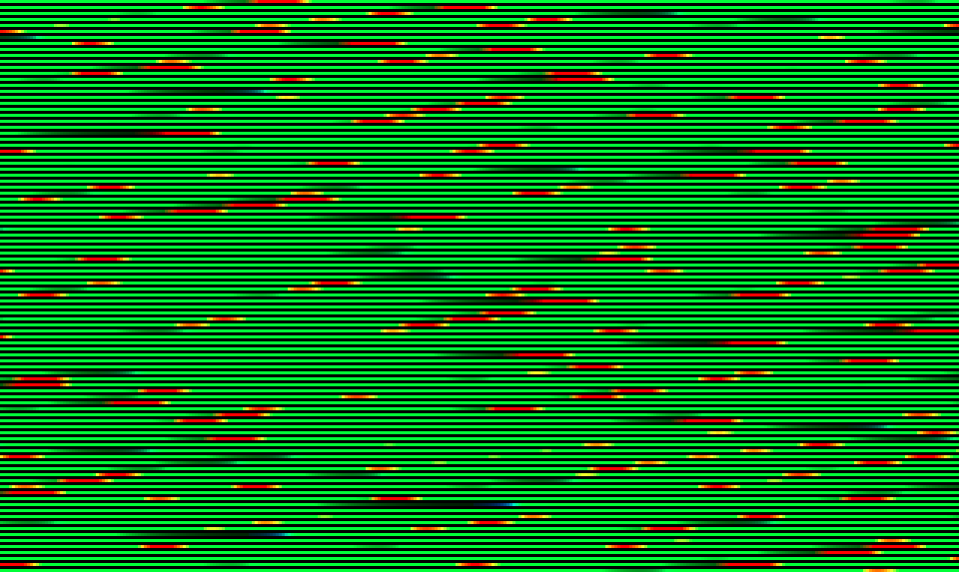
docs/lamp/opt-075.png
