gallicchio/ai_unleashes_chaos/docs/lamp/opt-078.png

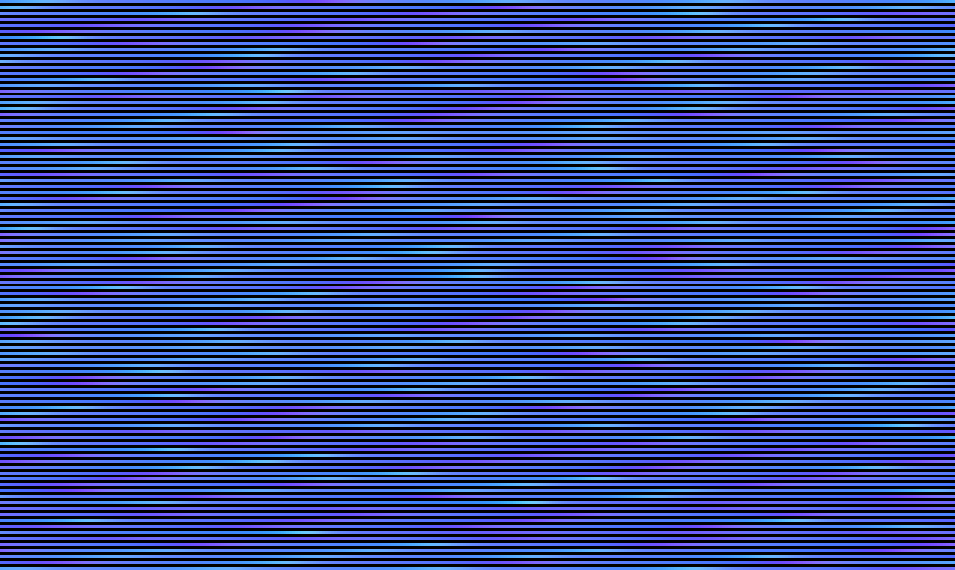
docs/lamp/opt-078.png
