gallicchio/ai_unleashes_chaos/docs/lamp/opt-079.png

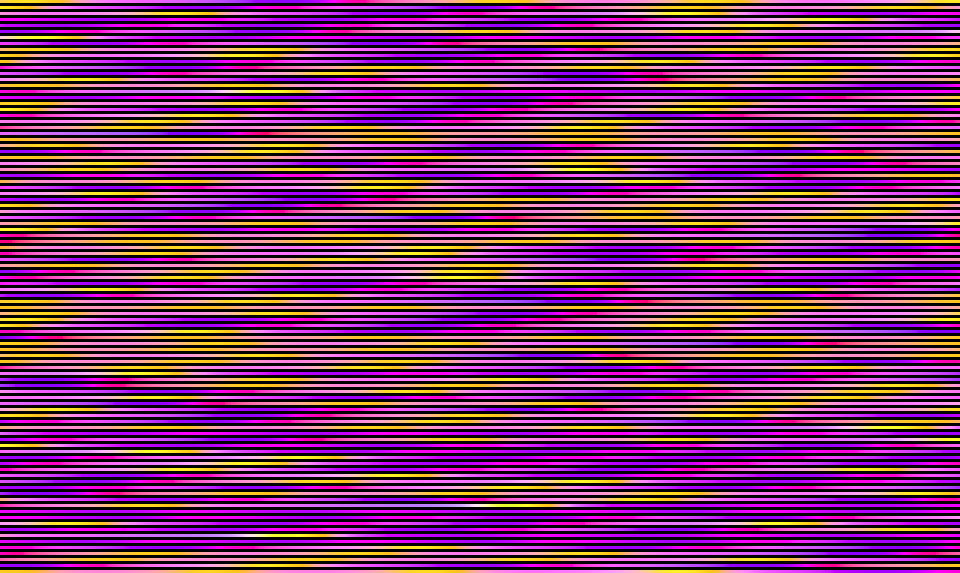
docs/lamp/opt-079.png
