gallicchio/ai_unleashes_chaos/docs/lamp/opt-080.png

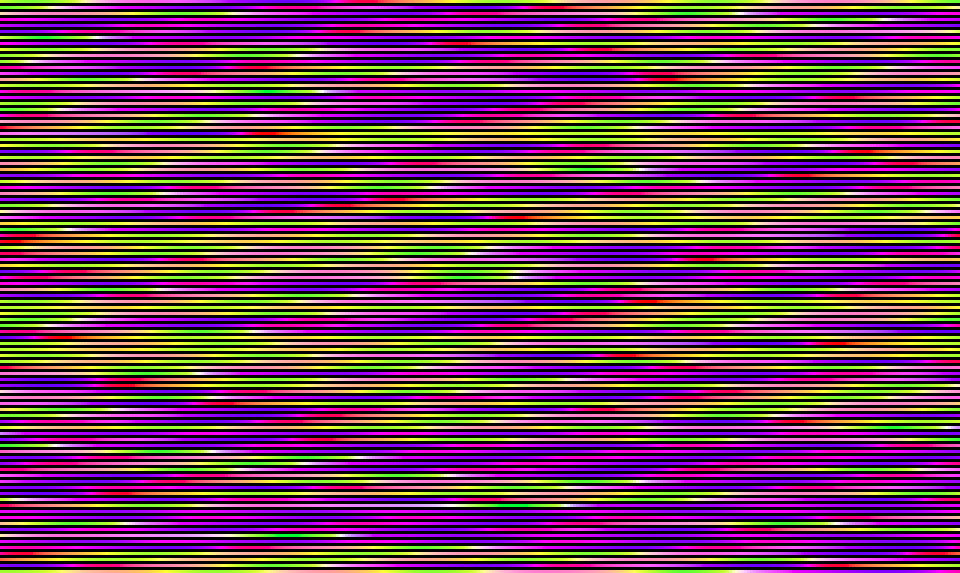
docs/lamp/opt-080.png
