gallicchio/ai_unleashes_chaos/docs/lamp/opt-081.png

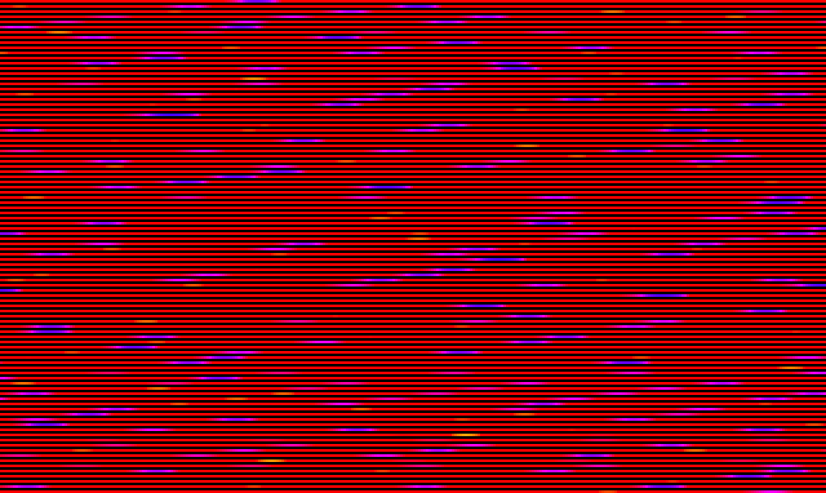
docs/lamp/opt-081.png
