gallicchio/ai_unleashes_chaos/docs/lamp/opt-082.png

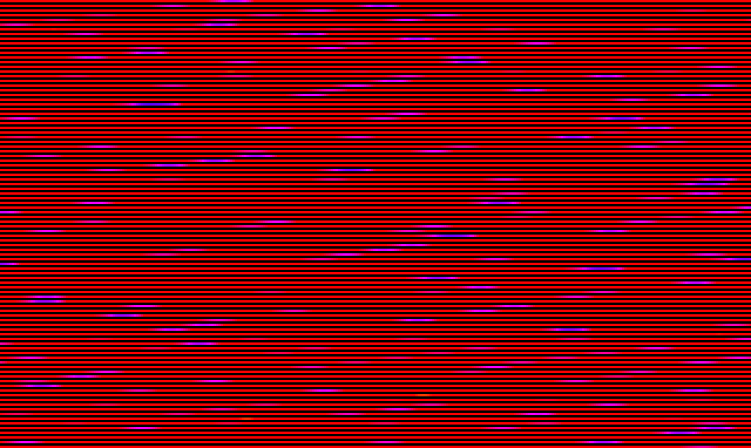
docs/lamp/opt-082.png
