gallicchio/ai_unleashes_chaos/docs/lamp/opt-083.png

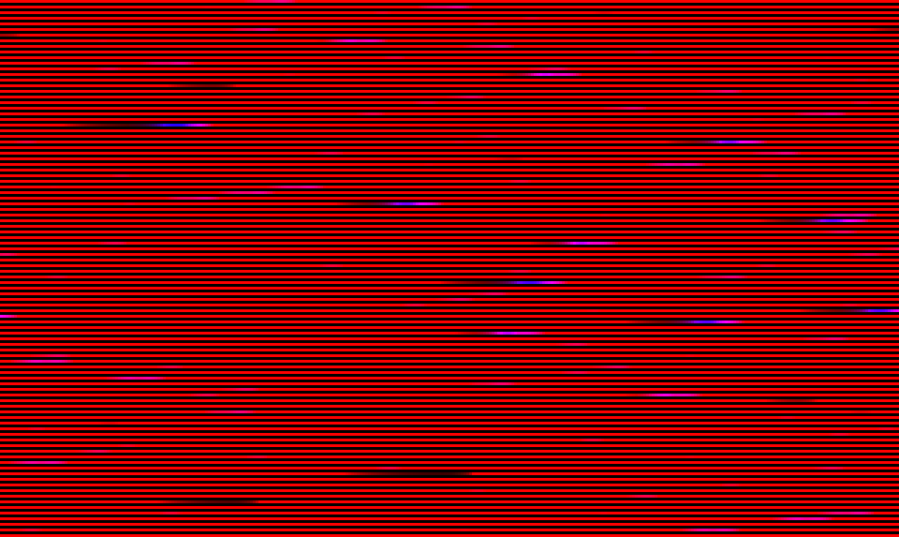
docs/lamp/opt-083.png
