gallicchio/ai_unleashes_chaos/docs/lamp/opt-084.png

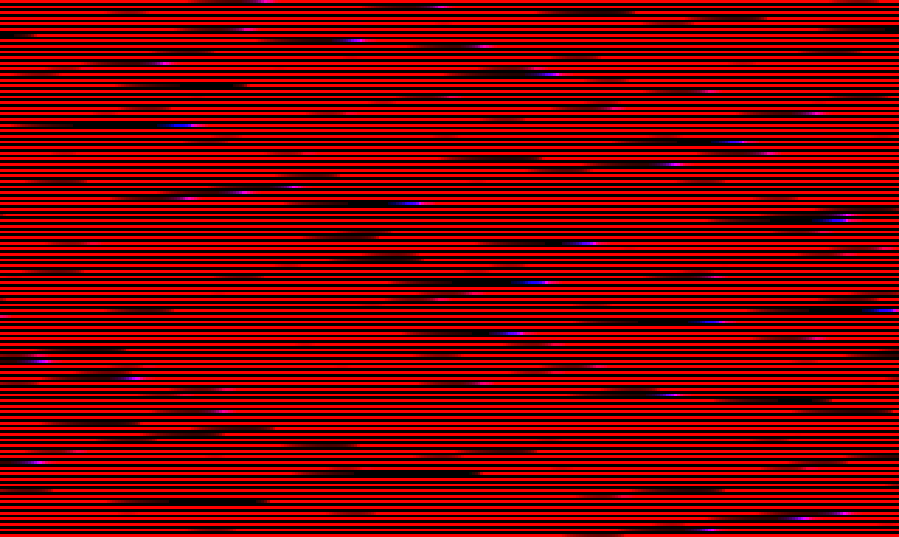
docs/lamp/opt-084.png
