gallicchio/ai_unleashes_chaos/docs/lamp/opt-086.png

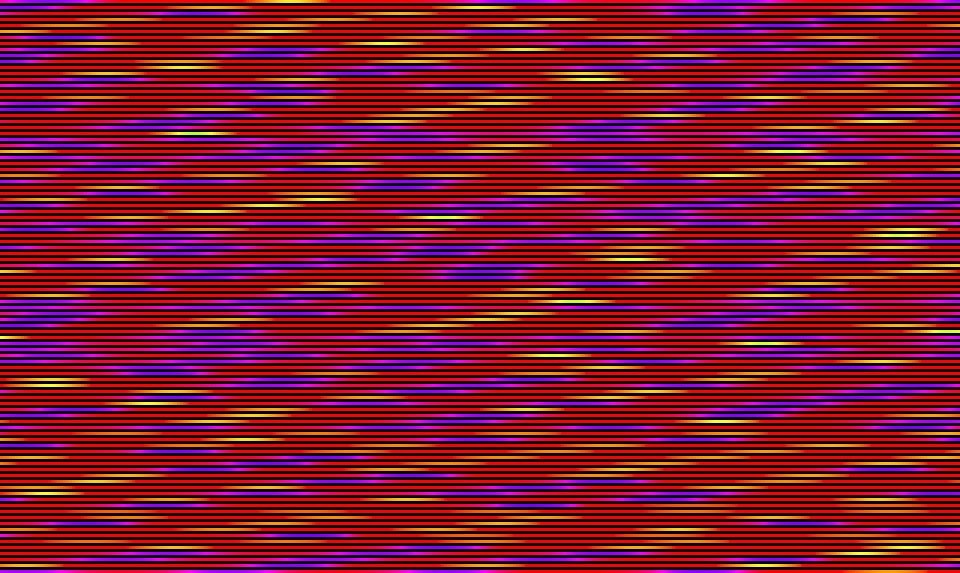
docs/lamp/opt-086.png
