gallicchio/ai_unleashes_chaos/docs/lamp/opt-087.png

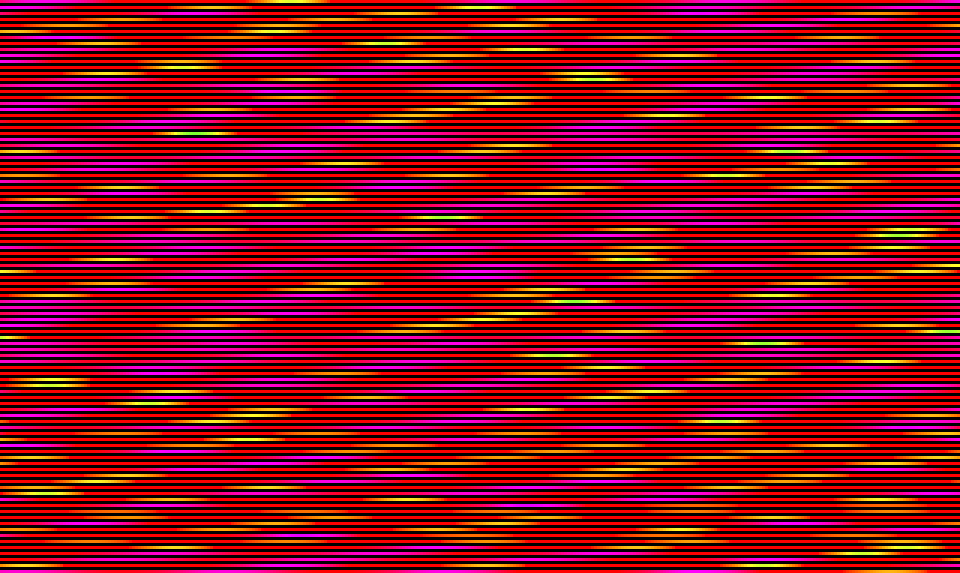
docs/lamp/opt-087.png
