gallicchio/ai_unleashes_chaos/docs/lamp/opt-089.png

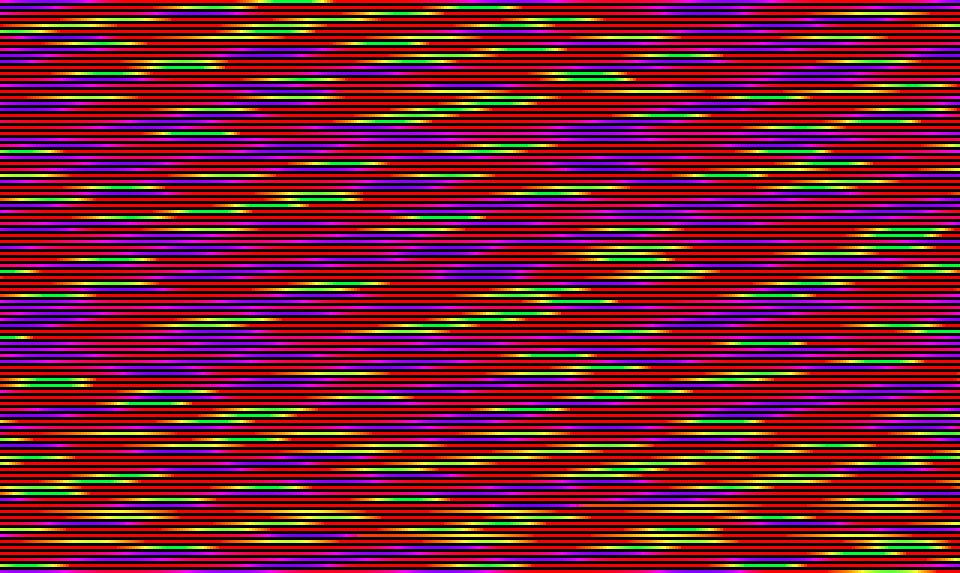
docs/lamp/opt-089.png
