gallicchio/ai_unleashes_chaos/docs/lamp/opt-090.png

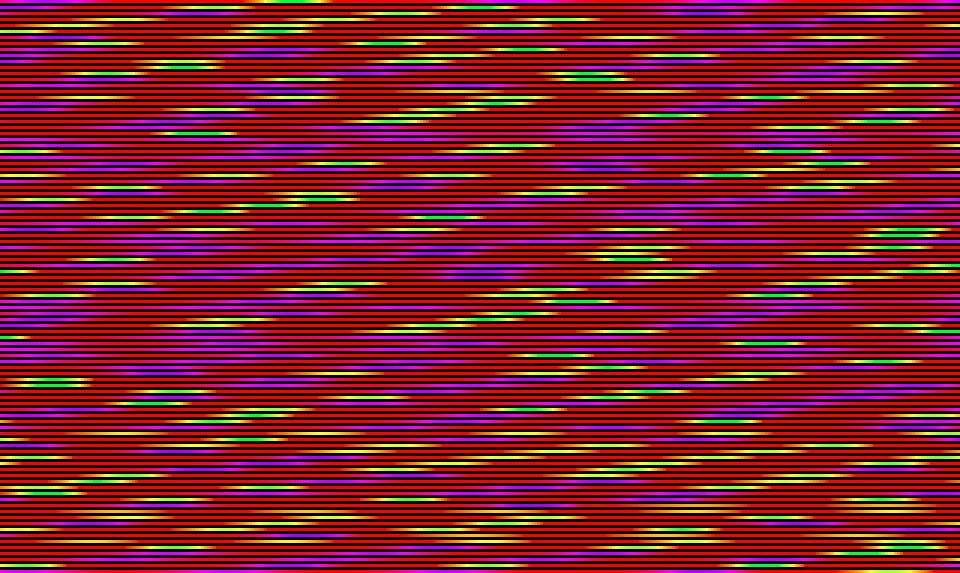
docs/lamp/opt-090.png
