gallicchio/ai_unleashes_chaos/docs/lamp/opt-091.png

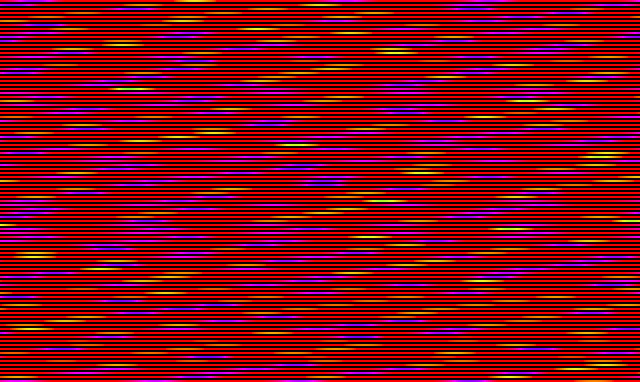
docs/lamp/opt-091.png
