gallicchio/ai_unleashes_chaos/docs/lamp/opt-092.png

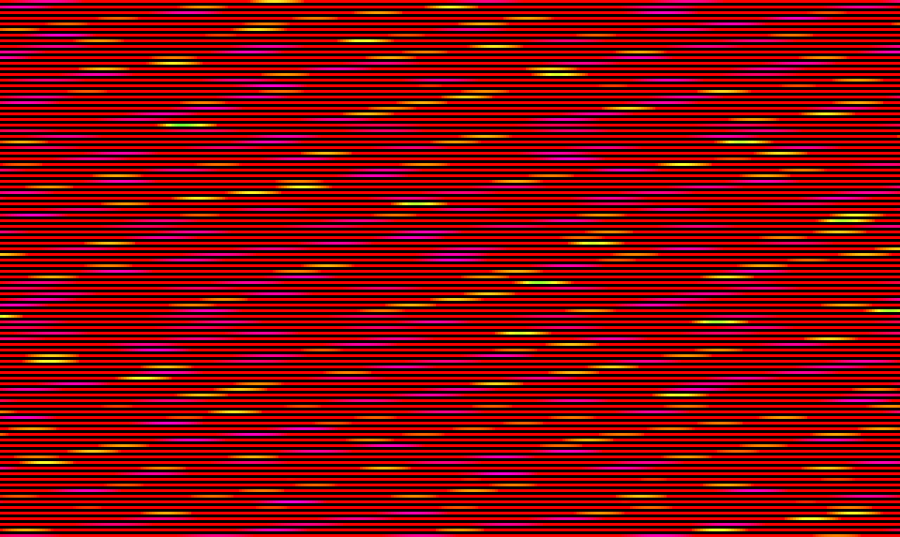
docs/lamp/opt-092.png
