gallicchio/ai_unleashes_chaos/docs/lamp/opt-094.png

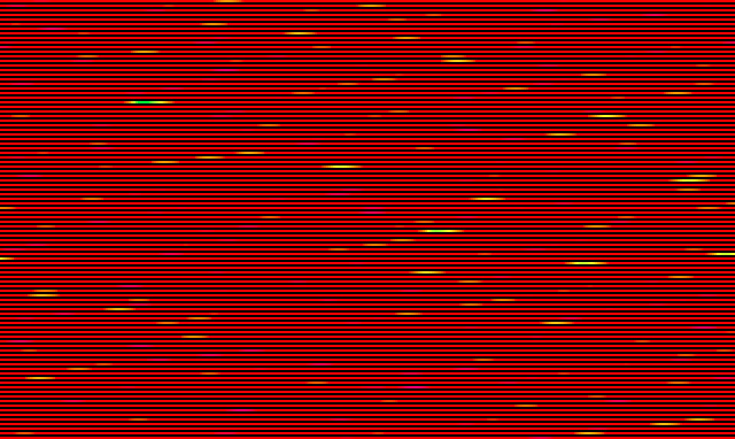
docs/lamp/opt-094.png
