gallicchio/ai_unleashes_chaos/docs/lamp/opt-096.png

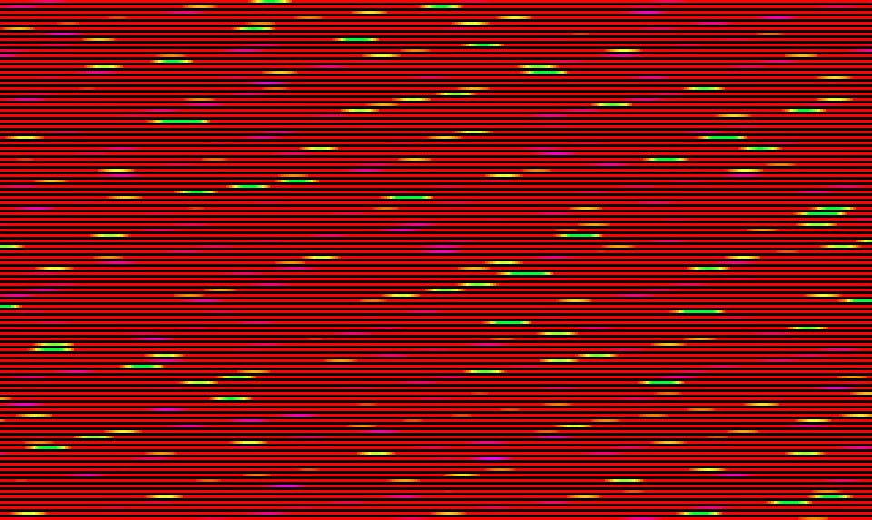
docs/lamp/opt-096.png
