gallicchio/ai_unleashes_chaos/docs/lamp/opt-097.png

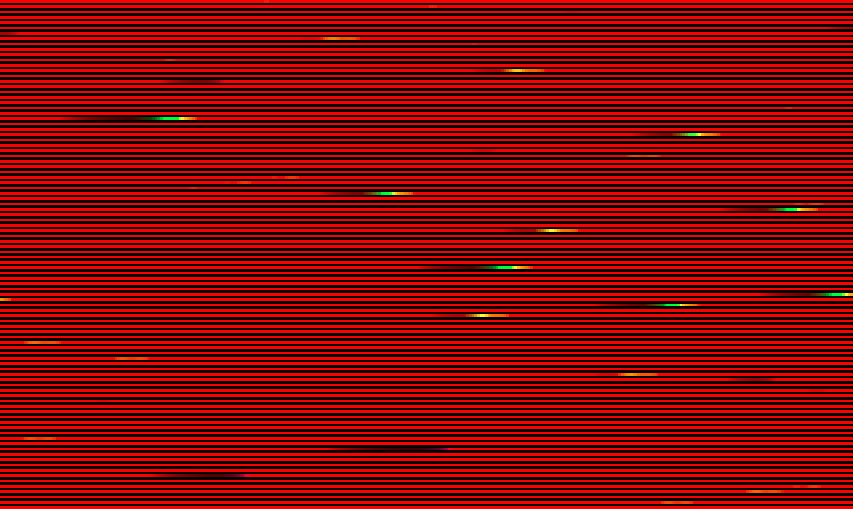
docs/lamp/opt-097.png
