gallicchio/ai_unleashes_chaos/docs/lamp/opt-098.png

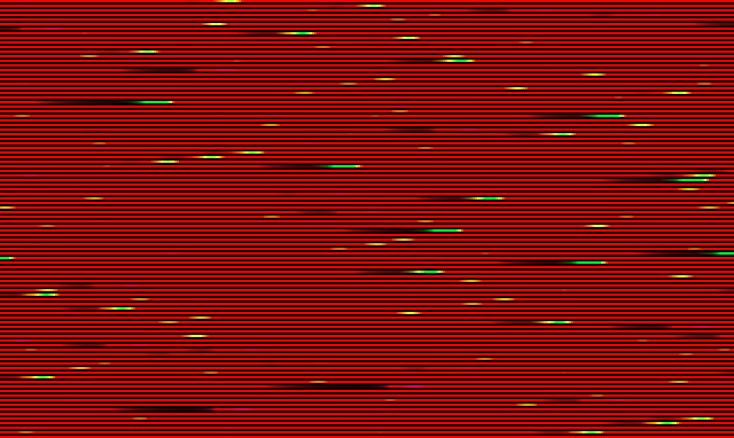
docs/lamp/opt-098.png
