gallicchio/ai_unleashes_chaos/docs/lamp/opt-099.png

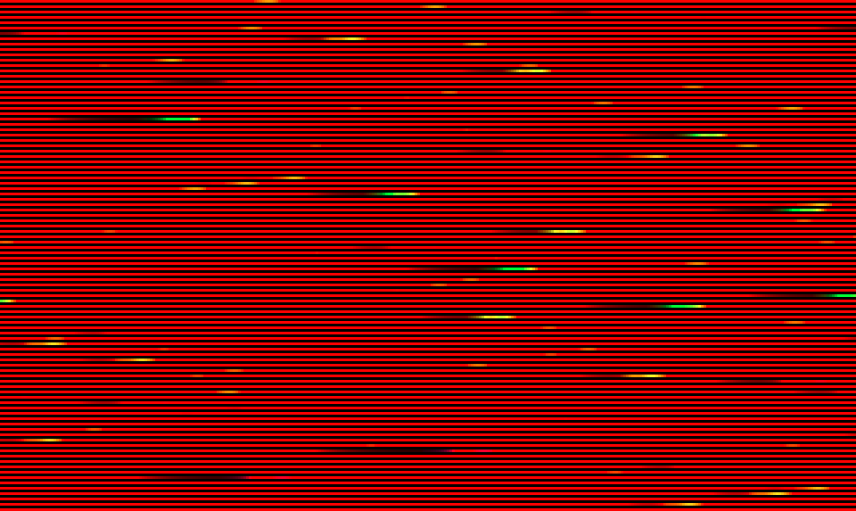
docs/lamp/opt-099.png
